MartijnScheer/Synthesizer/Documentatie 2024-2025/Input/Presentatie PCB Ontwerp Van Rick smelt en Patrick van Ommen.pdf

# Pulse soundworks

# Project synthesizer PCB Ontwerp

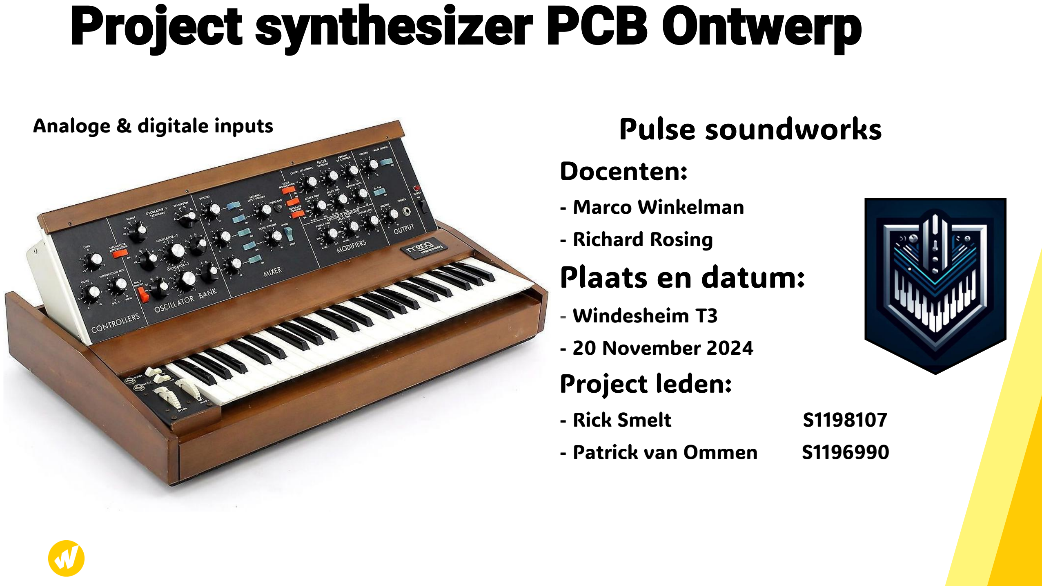
[picture p133: page 1]

# Docenten:

## - Marco Winkelman - Richard Rosing

# Plaats en datum:

## - Windesheim T3 - 20 November 2024

# Project leden:

- Rick Smelt | S1198107
- Patrick van Ommen | S1196990

## Analoge & digitale inputs

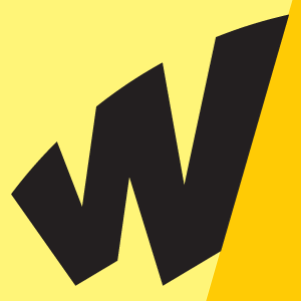
[picture p134: figure]

# Herhaling

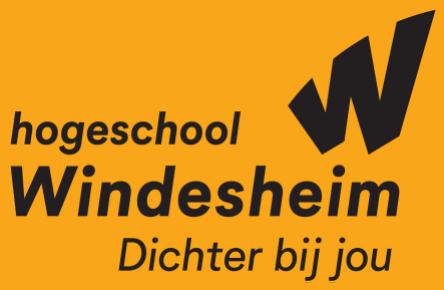
[picture p135: figure]

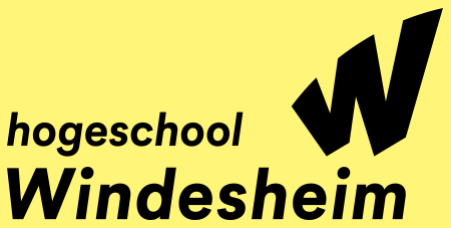
[picture p136: figure]

# wat is de opdracht?

❑Het ontwerpen en bouwen van een modulaire synthesizer.

### ❑ Er moet een analoge input en een midi input worden gemaakt en deze moet aangesloten

worden.
❑ Voor de analoge input wordt een keyboard gemaakt. En voor de midi input zal het digitale signaal worden omgezet naar een analoog signaal.
❑ Uit beide inputs zal een gate signaal komen en een toonhoogte. Deze beide signalen moeten

### naar de volgende modules:

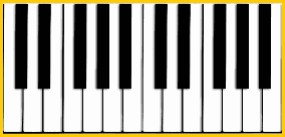
[picture p137: figure]
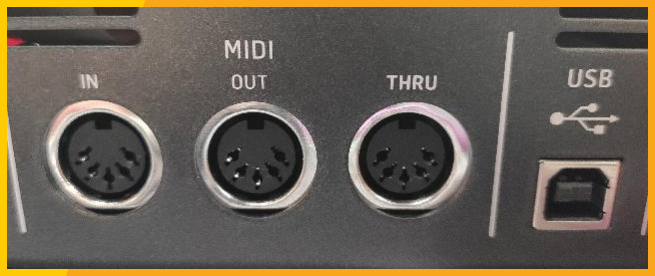
[picture p138: figure]

- ADSR- module
- Sequenser
- oscillator

# Achtergronden

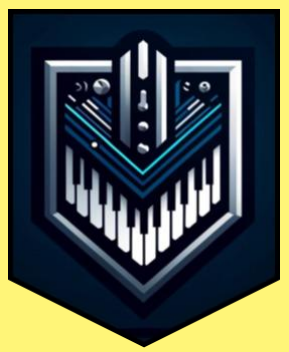
[picture p139: figure]

# Doelstelling:

# Project resultaten

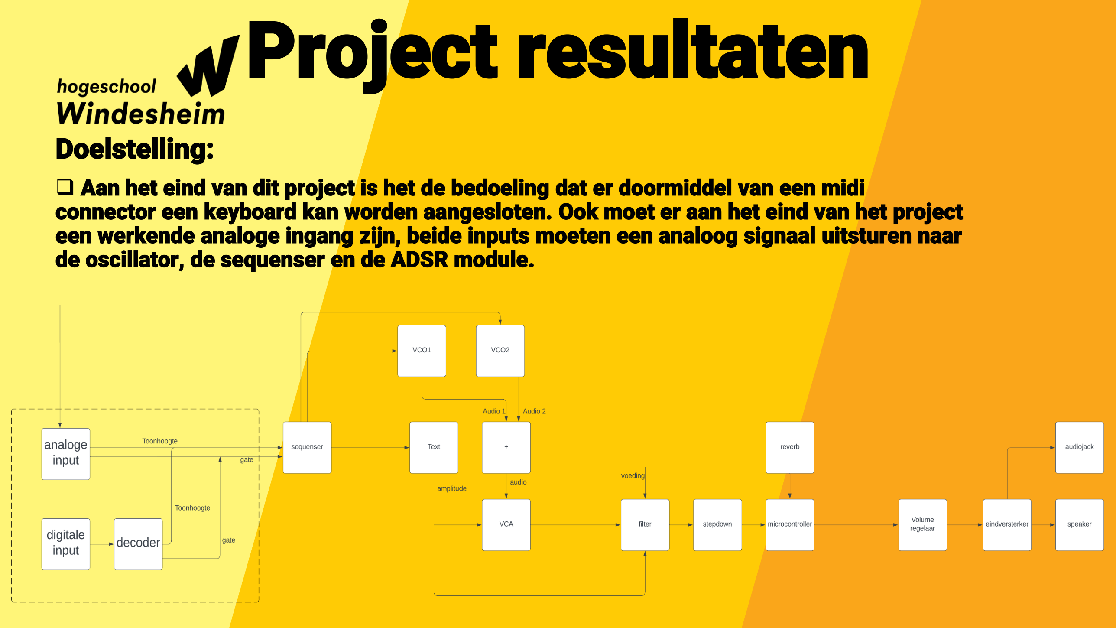
[picture p140: page 4]

## ❑ Aan het eind van dit project is het de bedoeling dat er doormiddel van een midi connector een keyboard kan worden aangesloten. Ook moet er aan het eind van het project een werkende analoge ingang zijn, beide inputs moeten een analoog signaal uitsturen naar

de oscillator, de sequenser en de ADSR module.

# Eisen Analoge input

Functioneel of niet functioneel | eis
Functioneel | Al is een toets ingedrukt en er word een volgende toets ingedrukt dient deze toon te worden afgespeeld en de initiële toon te stoppen.
Functioneel | Minimaal 1 octaaf aan toetsen waarbij er 4 octaven kunnen worden afgespeeld
Functioneel | Een analoog signaal voor de toonhoogte.
Functioneel | Een gate signaal moet worden verstuurd zodra een toets op het keyboard is ingedrukt of is losgelaten, dit signaal is uit: 0V en aan 3.3V
Functioneel | 1 octaaf krijgt een range van 1 volt.
Niet functioneel | Geen aanslag gevoeligheid
Niet functioneel | Een maximaal bedrag van 50 euro
Niet functioneel | De module moet samen kunnen werken met de andere groepen.
Niet functioneel | Het moet veilig en gemakkelijk in gebruik zijn

# Eisen Digitale input

Functioneel of niet functioneel | eis
Functioneel | Al is een toets ingedrukt en er word een volgende toets ingedrukt dient deze toon te worden afgespeeld en de initiële toon te stoppen.
Functioneel | De decoder zet het digitale midi signaal om naar een analoog signaal voor de toonhoogte.

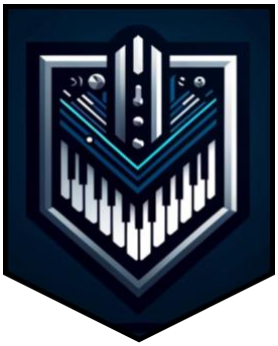
[picture p141: figure]

Functioneel | Een gate signaal moet worden verstuurd zodra een toets op het keyboard is ingedrukt of is losgelaten, dit signaal is uit: 0V en aan: 3.3V
Functioneel | Na de midi connector moet het digitale signaal worden verstuurt naar een decoder deze zet het midi signaal om naar een analoge signaal die overeen komt met het analoge input signaal
Functioneel | De midi input moet voor het grootste gedeelte voldoen aan het NEN-EN-INC 63035 protocol, daaronder valt dus geen aanslag gevoeligheid en opslaan van het signaal.
Niet functioneel | Geen aanslag gevoeligheid
Niet functioneel | Een maximaal bedrag van 50 euro
Niet functioneel | De module moet samen kunnen werken met de andere groepen.
Niet functioneel | Het moet veilig en gemakkelijk in gebruik zijn

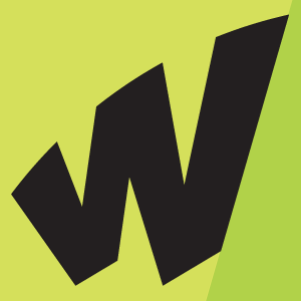
[picture p142: figure]

# PCB

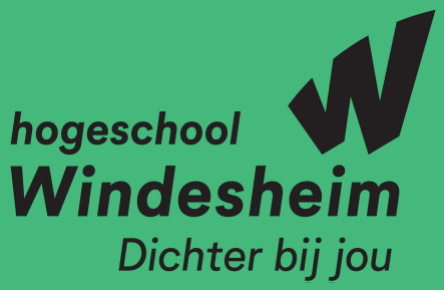
[picture p143: figure]

# SCHEMA PCB

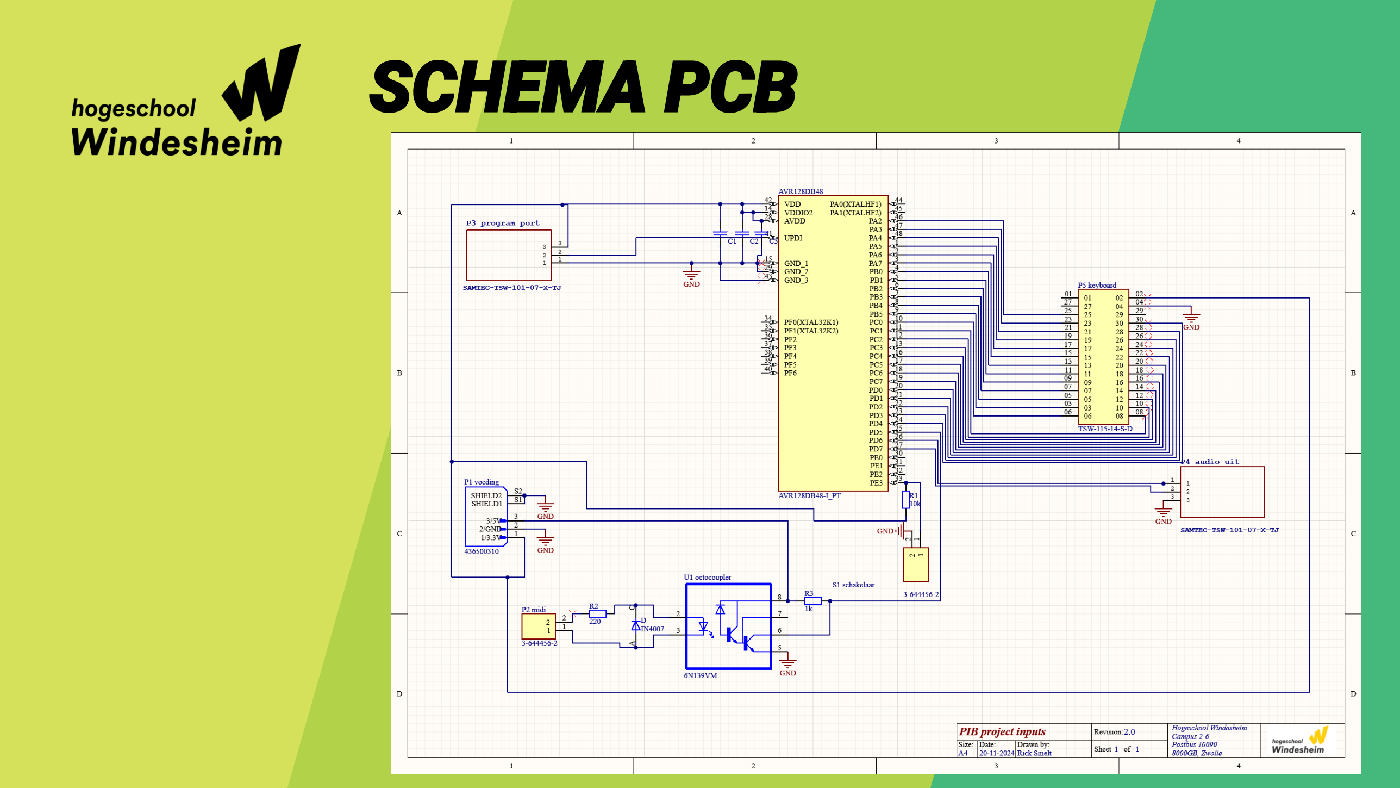
[picture p144: page 8]

DESIGN 2D | DESIGN 3D

# PCB DESIGN

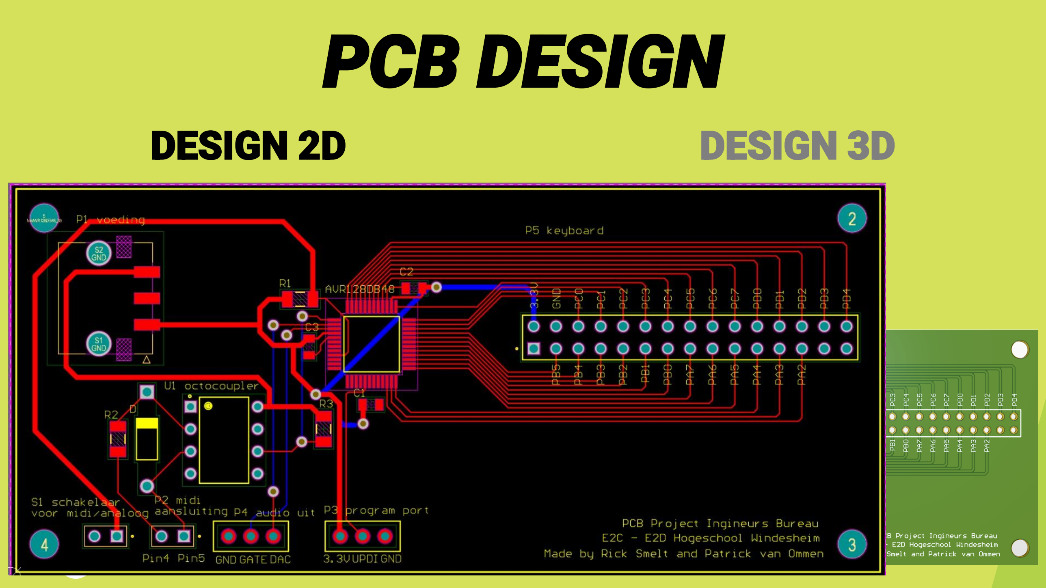
[picture p145: page 9]

DESIGN 2D | DESIGN 3D

# PCB DESIGN

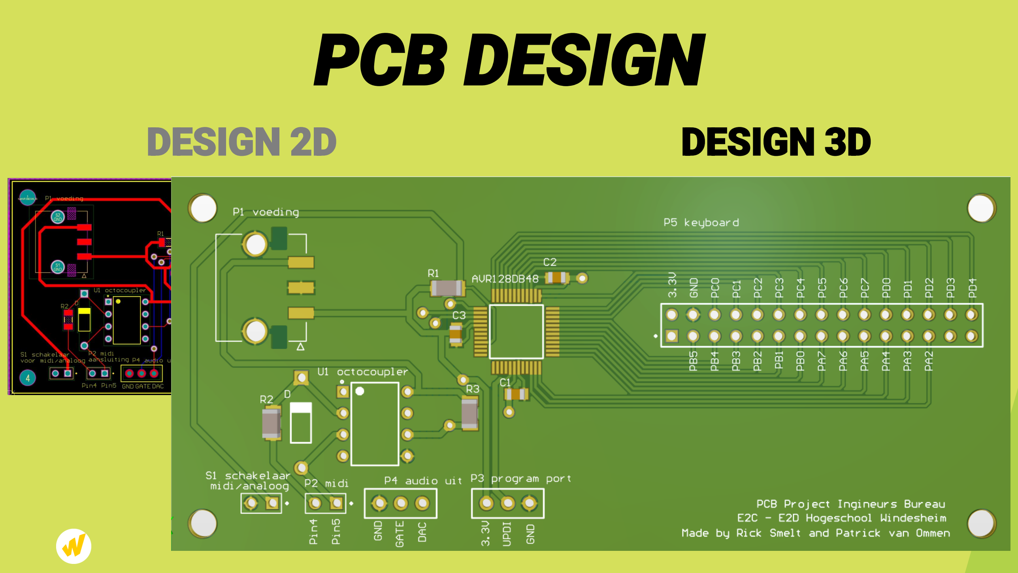
[picture p146: page 10]

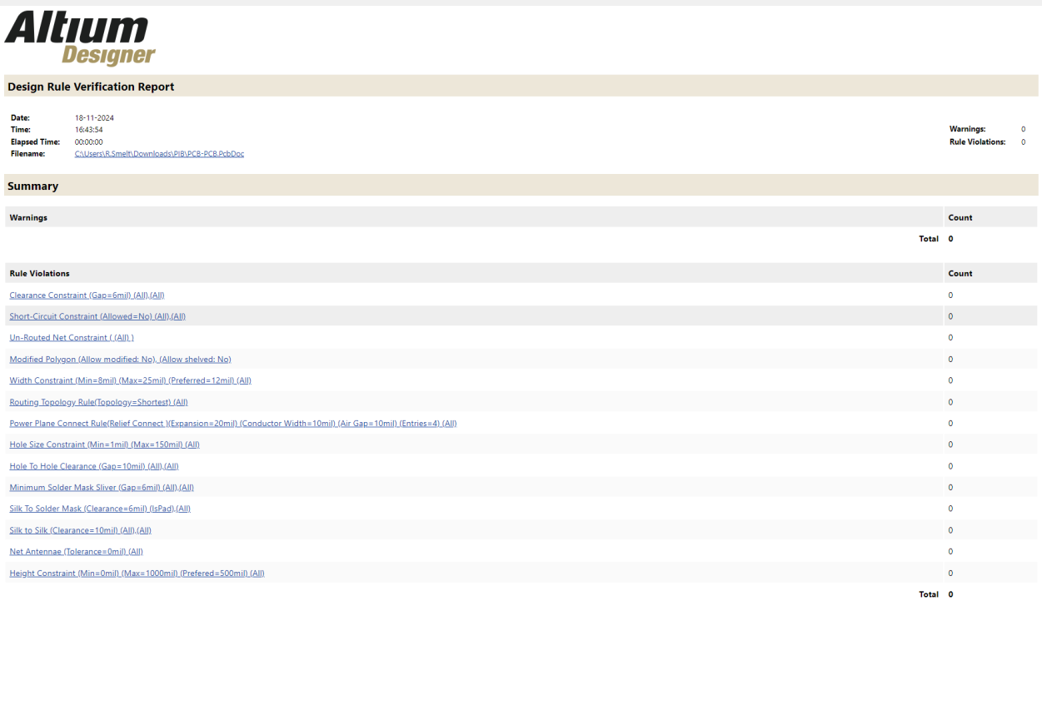
[picture p147: figure]

# - Alle rules die de fabrikant had aan het PCB zijn opgenomen in de rules van altium. De foto hiernaast geeft aan dat het PCB aan alle rules voldoet die de

fabrikant heeft opgesteld.

# DESIGN RULE CHECK / DESIGN RULE CHECK FABRIKANT

# KEUZE VAN PLAATSING COMPONENTEN

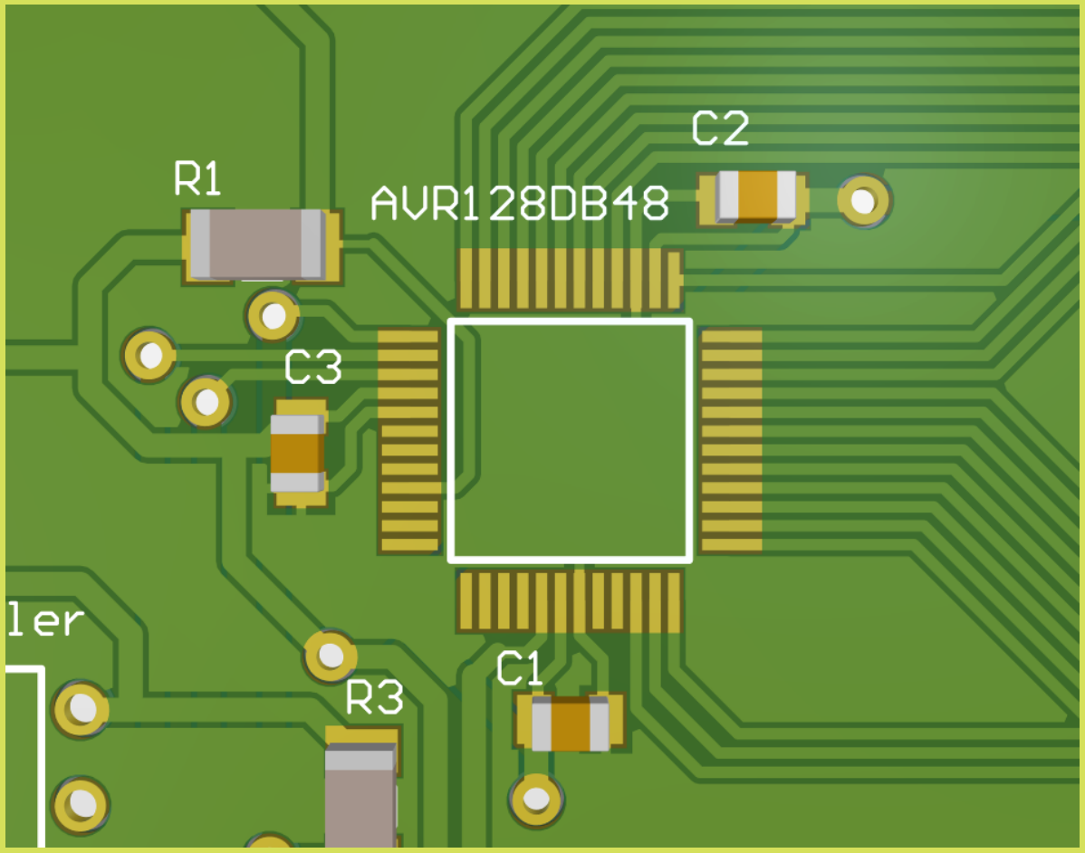
[picture p148: figure]

# KEUZE VAN PLAATSING COMPONENTEN

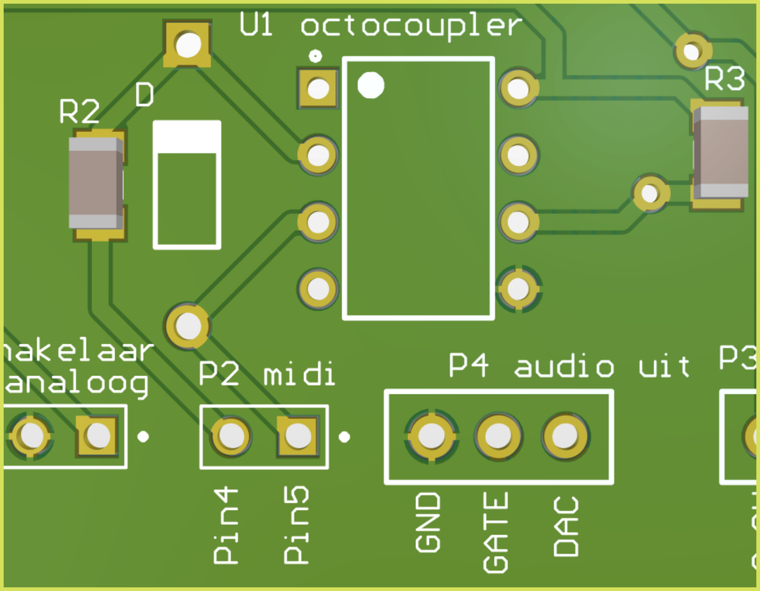
[picture p149: figure]

# KEUZE VAN PLAATSING COMPONENTEN

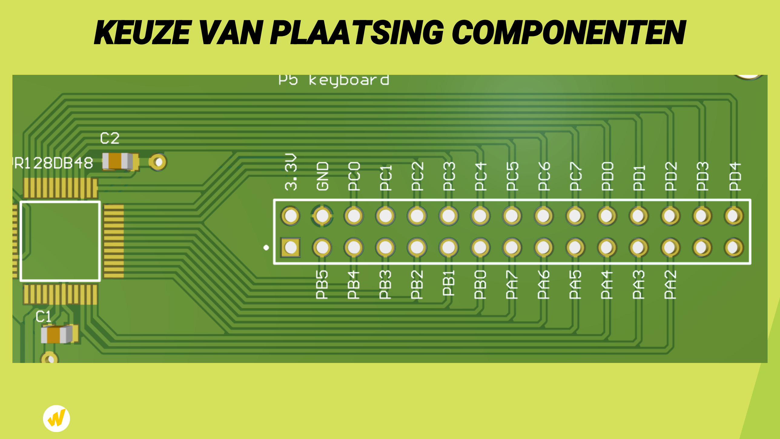
[picture p150: page 14]
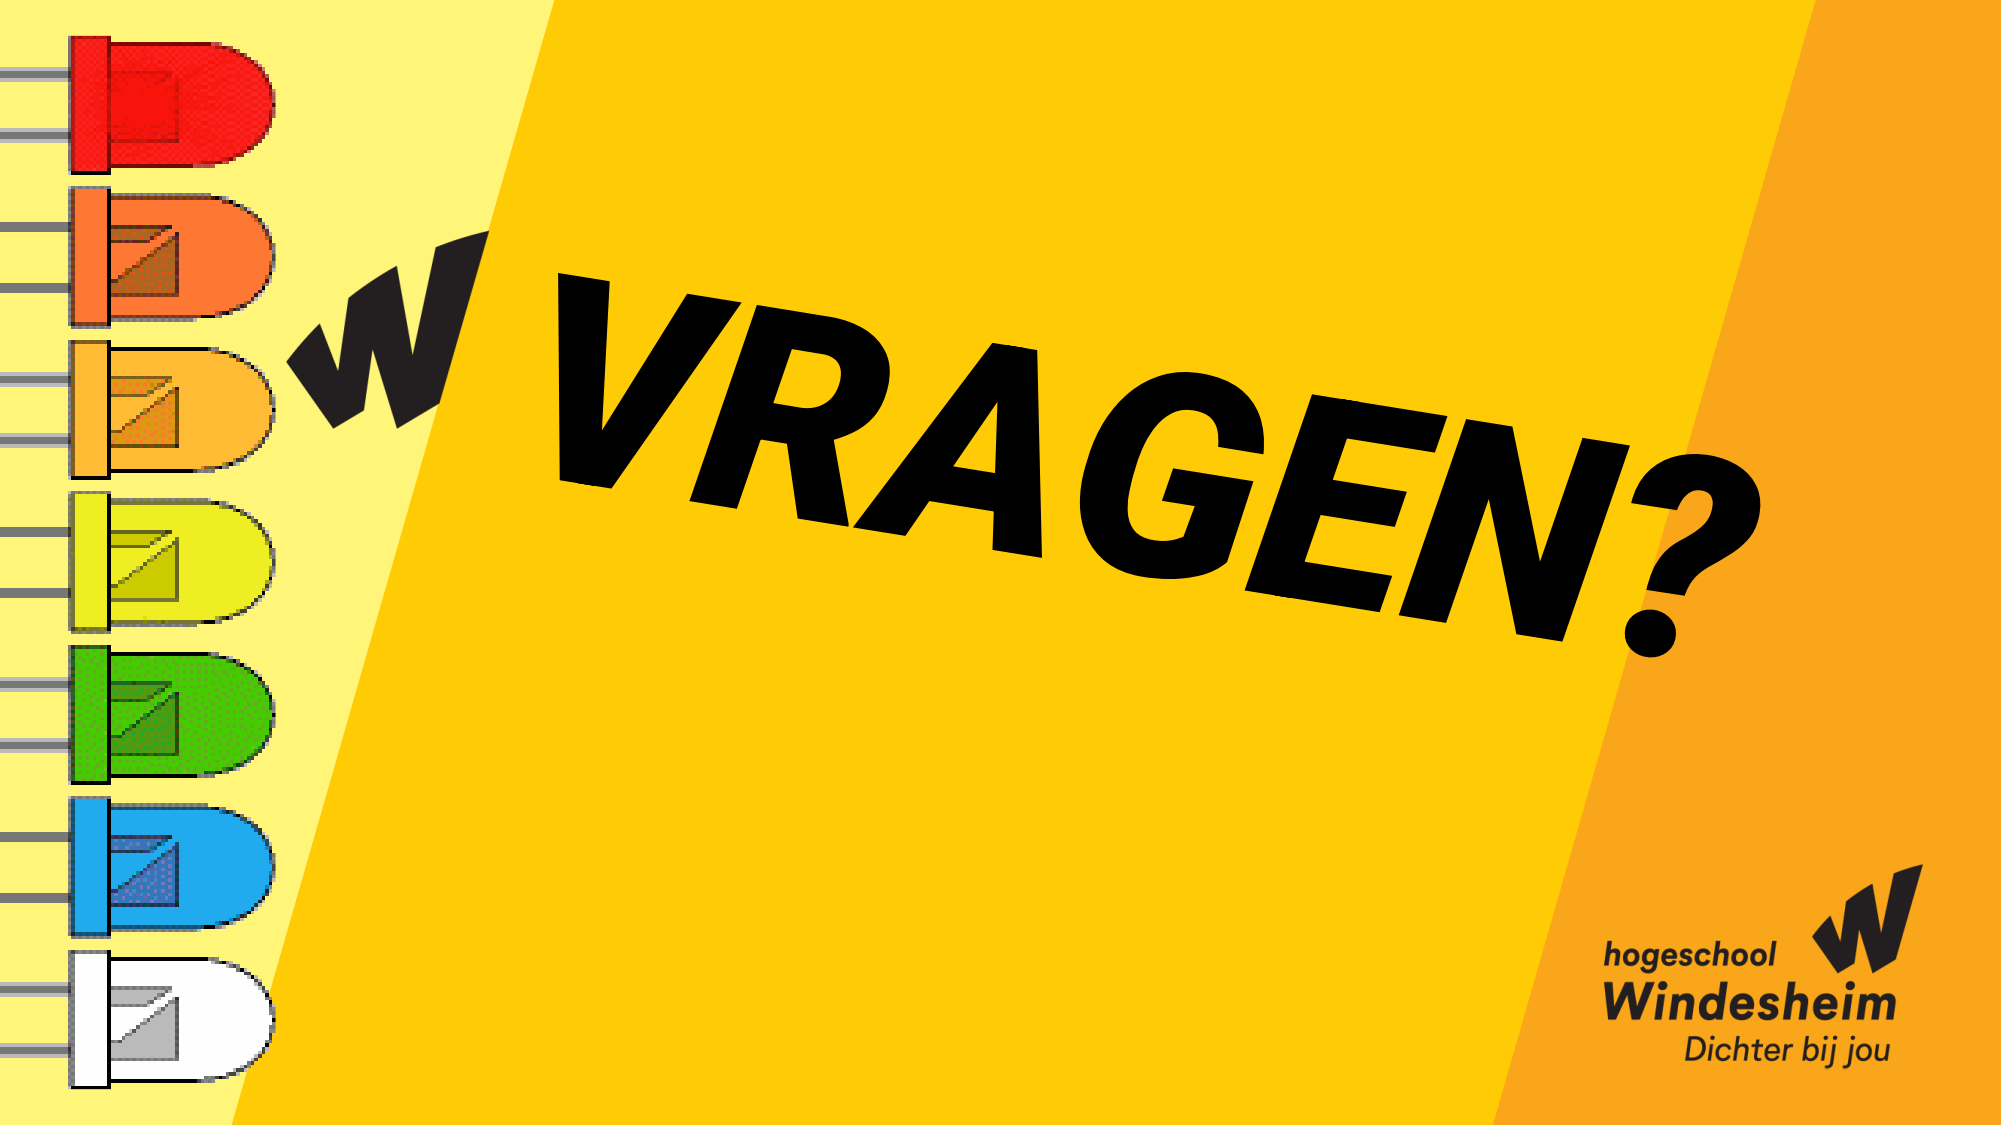
[picture p151: page 15]
