MartijnScheer/Synthesizer/Documentatie 2024-2025/Power amplifier + Power supply/Ontwerp/PIB Ontwerp Eindversterker en Voeding.pdf

# Concept

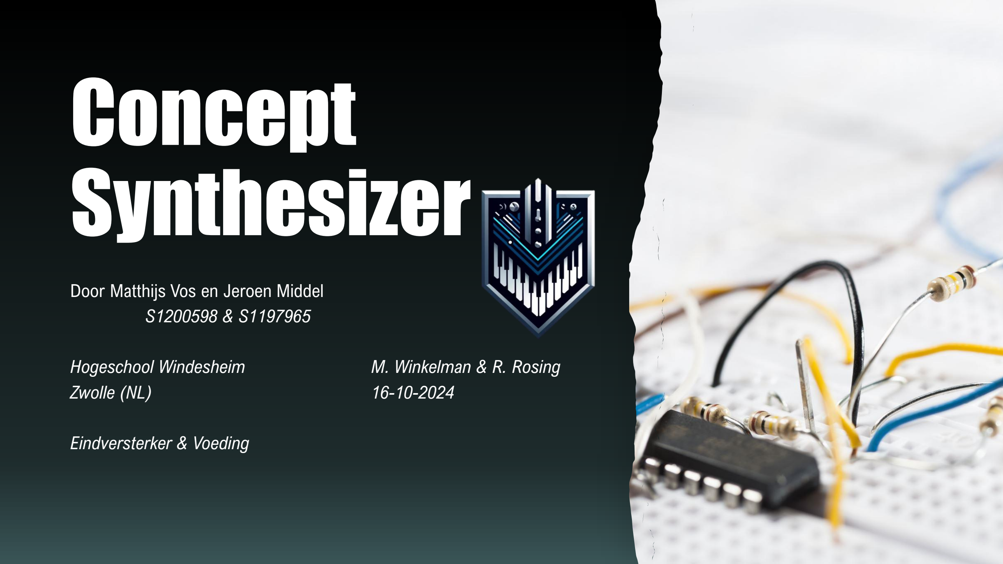
[picture p170: page 1]

# Synthesizer

### Door Matthijs Vos en Jeroen Middel

S1200598 & S1197965

Hogeschool Windesheim | M. Winkelman & R. Rosing
Zwolle (NL) | 16-10-2024

### Eindversterker & Voeding

# Plan van Eisen, Versterker

Eisen - Moet genoeg kunnen versterken voor een externe speaker van 8 ohm (functioneel) - Minimaal vermogen van de eindversterker is 1W eff (functioneel) - De modules voor de eindersterker moeten worden beschermd (niet-functioneel) - De gebruiker moet het volume kunnen aanpassen (functioneel) - De eindversterker mag niet te warm worden (passief, actief) (niet-functioneel) - Vervorming (1% harmonisch)(niet-functioneel)

## Wensen

- Meerdere soorten outputs (Speaker,

## audiojack) (niet-functioneel) - Over current protection voor de eindversterker en de voeding (niet-functioneel) - Beide modules de voeding en de versterker zo energiezuinig maken met minimale verliezen (niet-functioneel) - Beide modules zo compact mogelijke maken (niet-functioneel)

16-10-2024

# Ontwerp Eindversterker

## - Ingangsspanning maximaal 5 Vpp

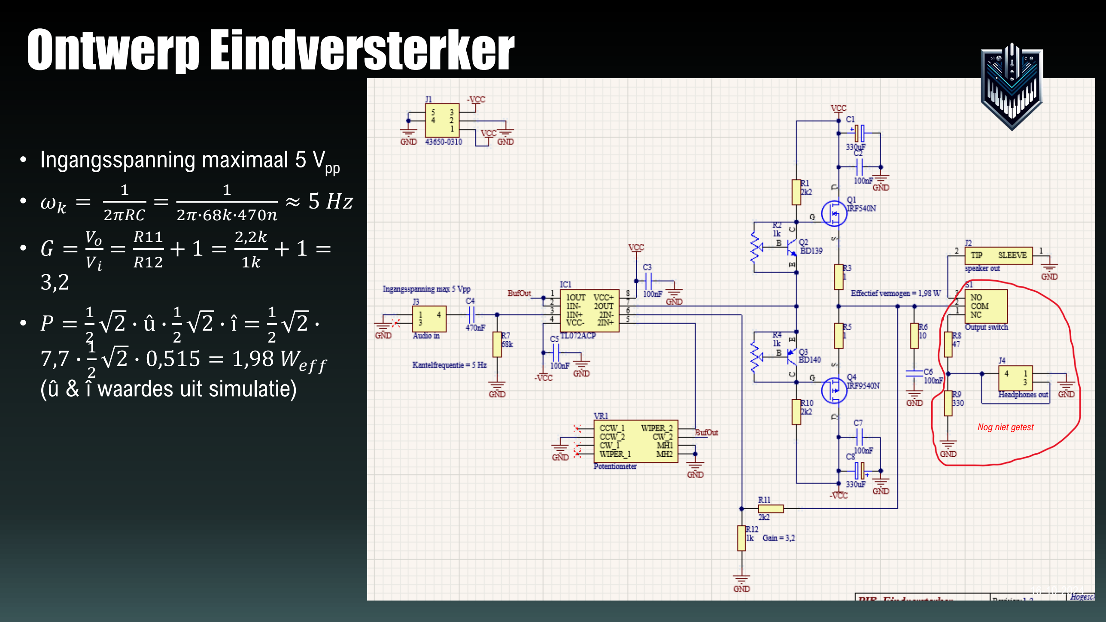
[picture p171: page 3]

- ωk =

1
2πRC

=

1
2π∙68k∙470n

≈ 5 Hz

- G =

Vo
Vi

=

R11
R12

+ 1 =

2,2k
1k

+ 1 =
3,2
- P =

1
2

2 ∙ û ∙

1
2

2 ∙ î =

1
2

2 ∙
7,7 ∙

1
2

## 2 ∙ 0,515 = 1,98 Weff

## (û & î waardes uit simulatie)

Nog niet getest

Kenmerk | MOSFET | BJT
Type | Spannings-gestuurd | Stroom-gestuurd
Besturing | Bestuurd door spanning op de gate | Bestuurd door basisstroom
Ingangsimpedantie | Hoog (meestal in de megaohms) | Laag (meestal in de kiloohms)
Stroomversterking | Kan zeer hoog zijn (afhankelijk van type, bv. N-kanalen of P-kanalen) | Lager, afhankelijk van de hFE-waarde (50 -500)
Verlies (Efficiency) | Lager bij hoogfrequente toepassingen | Hoger door basisstroom
Snelle schakeling | Sneller, vooral bij hoge frequenties | Langzamer vergeleken met MOSFET
Vermogensverlies | Lager omdat er minder inputstroom nodig is | Hoger vanwege hogere inputstroom
Thermisch gedrag | Minder gevoelig voor temperatuurvariaties | Gevoeliger voor temperatuurvariaties
Gebruik in vermogensschakelingen | Zeer geschikt voor hoge vermogens | Minder geschikt voor hoge vermogens
Kosten | Vaak duurder | Goedkoper
Toepassingen | Voornamelijk gebruikt in vermogenselektronica (bijv. voedingen, converters) | Gebruikt in lage-vermogenselektronica (bijv. versterkers)
Controle op aan/uit-stand | Eenvoudiger door de spanning op de gate | Moeilijker vanwege continue basisstroom nodig
Beschikbaarheid van modellen | N-kanaal en P-kanaal | NPN en PNP
Complexiteit van schakeling | Eenvoudiger ontwerp (minder componenten nodig) | Complexer ontwerp (meer componenten nodig)
Ruisgevoeligheid | Minder gevoelig voor ruis | Meer gevoelig voor ruis | 16-10-2024

# Vergelijk transistoren

# Vergelijk Bias

Type Diode | Werking | Kenmerken | Toepassingen | Complexiteit
Normale diode | Geleidt stroom in één richting (van anode naar kathode) en blokkeert in de andere richting | Voorwaartse spanning nodig om te geleiden (meestal 0,7V voor silicium, 0,3V voor germanium). Hoge doorslagspanning in omgekeerde richting. Laag spanningsverlies. | Gelijkrichtcircuits (AC naar DC omzetting), beveiliging tegen omgekeerde stroom, signaaldetectie en schakeling in elektronica. | Eenvoudig
Zenerdiode | Werkt als een normale diode in de voorwaartse richting, maar laat stroom door in omgekeerde richting bij een specifieke zenerspanning (bv. 5V) | Zenerspanning bepaalt de omgekeerde doorslagspanning. Stabiel bij deze spanning. Kan als spanningsreferentie werken en gecontroleerde omgekeerde stroom geleiden. | Spanningsreferenties in voedingen, beveiliging tegen spanningspieken, spanningsclamping, stabilisators in spanningsregelaarcircuits. | Matig
Variabele zenerdiode (VDR) | Gedraagt zich als een zenerdiode, maar de zenerspanning kan worden gevarieerd door een externe controle (zoals een potmeter of spanning) | Verstelbare zenerspanning afhankelijk van externe instellingen. Flexibele spanningsreferentie. Mogelijkheid om dynamisch de gewenste klemspanning in te stellen. | Instelbare spanningsregelaars, bescherming in schakelingen met veranderlijke spanningen, dynamische spanningsbeperking in voedingen of overspanningsbeveiligingen. | Complex

16

-10

-2024

# Vergelijk Spanningsversterker

Type Versterker | Werking | Kenmerken | Toepassingen | Complexiteit
Operationele versterker (opamp) | Een geïntegreerde schakeling (IC) die signalen versterkt door een verschilspanning tussen twee ingangen (inverting en non-inverting) te verwerken. | Zeer hoge versterkingsfactor. Hoge ingangsimpedantie, lage uitgangsimpedantie. Stabiele prestatie met weinig drift. Flexibel inzetbaar in meerdere configuraties (inverterend, niet-inverterend, comparator). | Audioversterkers, filters, signaalverwerking, spanningsvolgers, comparatoren. | Eenvoudig tot matig (opbouw in IC).

Discrete
transistorversterker

Gebruikt individuele
transistors (zoals BJT's
of MOSFET's) om
stroom te regelen en
een ingangssignaal te
versterken.

Configuratie kan flexibel
worden opgebouwd met
losse componenten.
Middelmatige tot hoge
versterkingsfactor,
afhankelijk van de
schakeling. Hoger
stroomverbruik en grotere
componenten. Meerdere
transistortrappen nodig voor grote versterking.

Basisaudioversterkers, RFversterkers,
vermogensversterkers in
vermogenstoepassingen.

Complex (moet zelf
ontworpen en
opgebouwd
worden).

# Controle eisen, Versterker

## Controle - Er komt het juiste geluid uit de speaker - Peff = 1,98 W in simulatie - Peff = … W IRL - Er zit een buffertrap in voor de versterker

## - Er zit een potmeter om het volume te regelen

## - Het breadbord smelt niet onder de schakeling weg

## - Er is geen vervorming op de scoop te zien

Eisen - Moet genoeg kunnen versterken voor een externe speaker van 8 ohm (functioneel) - Minimaal vermogen van de eindversterker is 1W eff (functioneel) - De modules voor de eindersterker moeten worden beschermd (niet-functioneel) - De gebruiker moet het volume kunnen aanpassen (functioneel) - De eindversterker mag niet te warm worden (passief, actief) (niet-functioneel) - Vervorming (1% harmonisch)(niet-functioneel)

# Plan van Eisen, Voeding

## Eisen

- Moet verschillende voltages kunnen leveren aan verschillende modules in de synthesizer (functioneel) - Moet symmetrisch voeding kunnen leveren van minimaal –10 tot +10 Volt (functioneel) - Moet asymmetrisch voeding kunnen leveren van minimaal +3,3 Volt (functioneel) - De voeding moet minimaal 80 mAmpère kunnen leveren aan elk van de modules (functioneel) - De voeding moet aan en uit kunnen worden gezet door de gebruiker (functioneel)

- De voeding mag niet te warm worden (passief,

## actief) (niet-functioneel) - Moet een lage rimpelspanning hebben (< 50mV) (niet-functioneel)

## - Eindversterker voeding minimaal 0.5 A (functioneel)

## Wensen

## - Over current protection voor de eindversterker en de voeding (niet-functioneel)

## - Beide modules de voeding en de versterker zo energiezuinig maken met minimale verliezen (niet-functioneel) - Beide modules zo compact mogelijke maken (niet-functioneel)

# Ontwerp Voeding

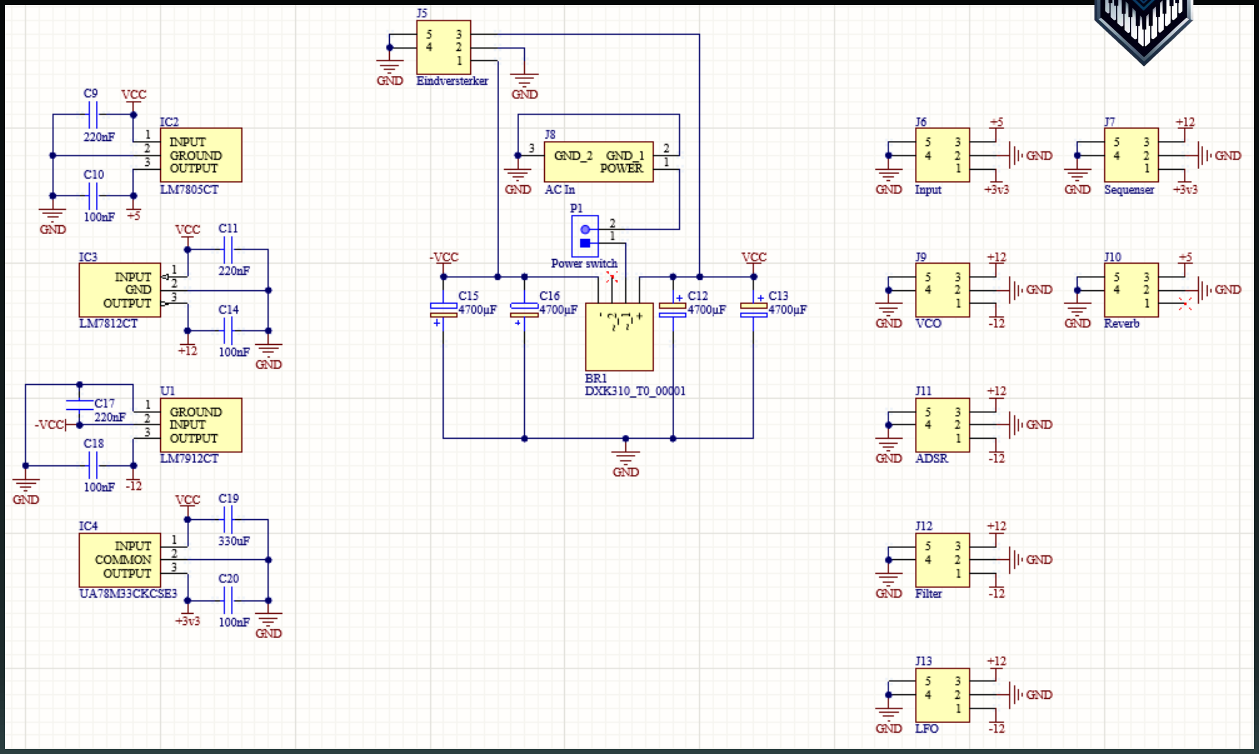
[picture p172: figure]

# Vergelijk type gelijkrichters

Type Gelijkrichter | Werking | Kenmerken | Toepassingen | Complexiteit
Enkelzijdige gelijkrichter | Gebruikt één diode om alleen de positieve halve golf van een wisselspanning door te laten, terwijl de negatieve helft wordt geblokkeerd. | Eenvoudig ontwerp. Verliest de helft van het AC -signaal (negatieve halve golf). Gemiddelde gelijkspanning is lager, en er is meer rimpel in de uitgangsspanning. Alleen de positieve halve golf wordt gebruikt, waardoor de efficiëntie lager is. | Lage -vermogenstoepassingen, eenvoudige voedingen, basis AC naar DC omzettingen. | Eenvoudig.
Dubbelzijdige gelijkrichter (2 diodes, middenaftakking) | Gebruikt twee diodes in combinatie met een transformator met een middenaftakking om zowel de positieve als de negatieve halve golf van de wisselspanning om te zetten in een gelijkspanning. | Maakt gebruik van een transformator met een middenaftakking, waarbij elke diode één helft van de wikkeling verwerkt. Minder componenten (2 diodes), maar de piekspanning is de helft van de secundaire spanning. | Voedingen met lagere vermogens, toepassingen waar een transformator met middenaftakking beschikbaar is. | Matig.
Dubbelzijdige gelijkrichter (4 diodes, brugschakeling) | Gebruikt vier diodes in een brugschakeling om zowel de positieve als de negatieve halve golf van de wisselspanning om te zetten in gelijkspanning. | Geen middenaftakking nodig. Volledige AC -golf wordt gebruikt, wat zorgt voor hogere efficiëntie en een hogere gemiddelde gelijkspanning. Hogere uitgangsspanning met minder rimpel. Meer componenten (4 diodes). | Voedingen met hogere vermogens, efficiëntere AC naar DC omzettingen, toepassingen waar een stabiele gelijkspanning nodig is. | Complex.

16

-10

-2024

# Controle Eisen, Voeding

## Eisen

- Moet verschillende voltages kunnen leveren aan verschillende modules in de synthesizer (functioneel) - Moet symmetrisch voeding kunnen leveren van minimaal –10 tot +10 Volt (functioneel) - Moet asymmetrisch voeding kunnen leveren van minimaal +3,3 Volt (functioneel) - De voeding moet minimaal 80 mAmpère kunnen leveren aan elk van de modules (functioneel) - De voeding moet aan en uit kunnen worden gezet door de gebruiker (functioneel)

- De voeding mag niet te warm worden (passief,

## actief) (niet-functioneel) - Moet een lage rimpelspanning hebben (< 50mV) (niet-functioneel)

## - Eindversterker voeding minimaal 0.5 A (functioneel)

Controle - Kan verschillende voltages leveren - Kan symmetrisch -12 tot +12 Volt leveren - Kan asymmetrisch +5 Volt leveren - Kan 80 mAmpère leveren aan alle modules binnen de synthesizer - Er is een aan en uit knop aanwezig - Het breadbord/breadbord kabels smelten niet - De rimpelspanning is maximaal 400mV - De eindversterker kan 0.5 A krijgen van de voeding

# Demo!!
