MartijnScheer/Synthesizer/Documentatie 2024-2025/README

Deze mappen bevatten de documentatie van de modules zoals ze waren in 2024-2025. 
Wees bewust dat deze documentatie op het moment van lezen kan zijn verouderd door mogelijke veranderingen in de synthesizer.
