MartijnScheer/Synthesizer/Documentatie Minor Project Synthesizer Hidde Huysmans & Martijn Scheer 2026/README

Documentatie van het Minor Project Synthesizer Hidde Huysmans & Martijn Scheer.
