MartijnScheer/Synthesizer/Documentatie Minor Project Synthesizer Hidde Huysmans & Martijn Scheer 2026/GitHub Documentatie/Readme

Documentatie van de GitHub zoals deze door ons is ingericht aan het einde van het 2026 elektronica project, dit mapje is puur ter documentatie voor het nakijken.
Voor projectgroepen is deze map niet van belang.
