MartijnScheer/Synthesizer/Documentatie 2024-2025/Filter/READ ME.txt

Om het bestand te kunnen openen
- Ga naar: https://app.diagrams.net/
- Druk op "bestaand diagram openen".
- Selecteer het .drawio bestand in deze map.
