MartijnScheer/Synthesizer/Documentatie Minor Project Synthesizer Hidde Huysmans & Martijn Scheer 2026/Software/Readme

De software per 06-2026. De laatste versie die wij hebben bewerkt.
