MartijnScheer/Synthesizer/Documentatie Minor Project Synthesizer Hidde Huysmans & Martijn Scheer 2026/Vooronderzoekje polyfoon/readme

Vooronderzoekje voor het omzetten van de huidige inputmodule naar een polyfoon systeem
