MartijnScheer/Synthesizer/Documentatie 2024-2025/LFO/README

Bestanden voor de LFO module gemaakt door Ruben Boeve
