MartijnScheer/Synthesizer/Documentatie 2024-2025/Sequencer/README

Bestanden voor de Sequencer module gemaakt door Roelof Zijda en Reinout Strating
