MartijnScheer/Synthesizer/Documentatie 2024-2025/Input/README

Bestanden voor de input module van de Synthesizer gemaakt door Rick Smelt en Patrick van Ommen
