MartijnScheer/Synthesizer/Documentatie 2024-2025/VCO/VCO concepten Ralph en Thijn V2.pptx

## Modulaire Synthesizer, VCO Concepten.

Thijn Berkhoff – 1198746
Ralph Hänninger – 1197535
Begeleid door Marco Winkelman

Mijn startpagina

25-9-2024
Zwolle

## Inhoudsopgave

Inleiding
Eisen en beperkingen
Conceptoplossing
Vergelijking concepten

## Inleiding

Opdracht:
Samen met de andere modules een synthesizer maken.
Doelstelling:
Het ontwerpen en designen van een volledige VCO module

## Slide 4

Eisen | functioneel | Niet-functioneel | verplicht | optioneel | prioriteit
1v/octaaf | x | | x | | 1
stroombeveiliging | | x | x | | 1
2 uitgangssignalen | x | | x | | 1
Bescherming in- en outputs | | x | x | | 1
PCB zo klein mogelijk | | x | | x | 3
Blok, driehoek en zaagtand signaal | x | | x | | 2
Moet samenwerken met andere modules | x | | x | | 1
Elektronica moet zichtbaar zijn | | x | x | | 3
Enige middelen tegen warmtevervoming | | x | | X | 3
Instelbare lineariteit en zaagsignaal | x | | | x | 2

## Slide 5

Beperkingen

Stroom en spanningslimieten.
Budget van 50 euro.
Geen kant en klare componenten. (devboards, Modules ETC)
Uiteindelijke afmetingen van het volledige design.

## Concept oplossingen

- Concept 1

Zaagtand oscillator als kern, andere signalen worden daaruit gemoduleerd.
Gebaseerd op een comparator / integrator opamp schakeling.

- Concept 2

Relaxation oscillator als kern, zaagtand wordt gemoduleerd uit blok of driehoek.
Geïnspireerd door “Electronics a system approach” van Neil Storey

## Concept 1

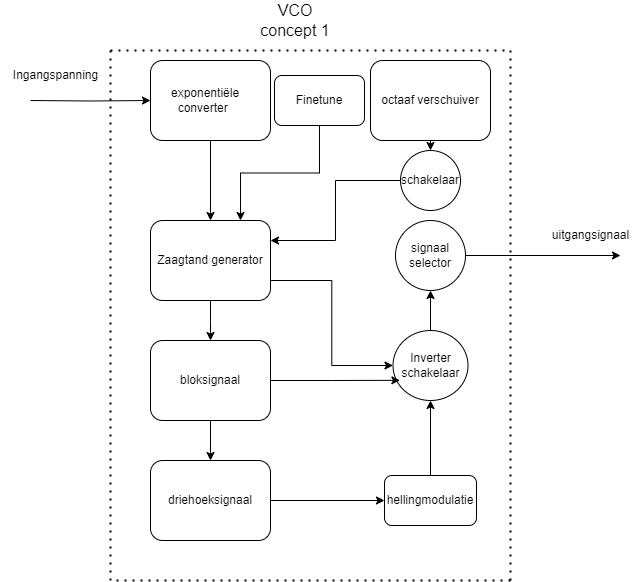
[picture p173: figure]

## Conceptschakeling 1

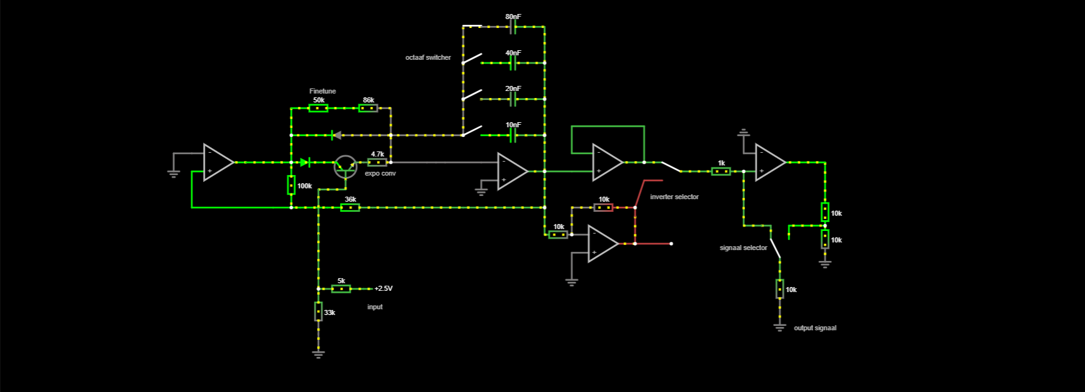
[picture p174: figure]

- Gesimuleerd op falstad.com
- Mist nog driehoek generator en hoekmodulatie
- Voldoet nog niet volledig aan eisen maar dat zou veranderd kunnen worden

## Concept 2

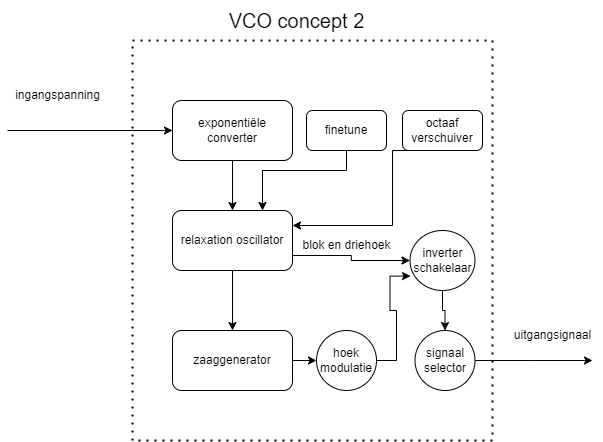
[picture p175: figure]

## Vergelijking concepten

- Concept 1

- Gebruikt 2 opamps voor de kern
- Iets ingewikkelder design
- Finetune en zaagsignaal makkelijker te bereiken
- Flexibeler door zaagsignaal als kern
- Onder 50 euro

- Concept 2

- Gebruikt 1 opamp voor de kern
- Wat minder ingewikkeld
- Zaagsignaal en finetune moeilijker te bereiken
- Minder flexibel want blok- en driehoeksignaal als kern
- Onder 50 euro

## Voorkeur Concept 1

- Zaagsignalen zijn makkelijker om te zetten naar andere signalen
- Flexibeler
- Conceptschakeling voldoet (bijna) aan de eisen
- Interessantere uitdaging
- Onder 50 euro

## Einde
