MartijnScheer/Synthesizer/Documentatie 2024-2025/Input/Systeemdossier uitleg.docx

# PCB Ontwerp

Dit zijn de Altium bestanden.

https://liveadminwindesheim-my.sharepoint.com/personal/s1198107_student_windesheim_nl/Documents/School/Jaar%202/Project%20synthensizer/Systeem%20Dossier/PIB%20PCB%20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

# CODE

Dit is het code bestand voor in MPLAB X IDE.

https://liveadminwindesheim-my.sharepoint.com/personal/s1198107_student_windesheim_nl/Documents/School/Jaar%202/Project%20synthensizer/Systeem%20Dossier/PIB_Code_Inp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

# Presentaties

## PVA

Dit is de PVA Presentatie.

https://liveadminwindesheim-my.sharepoint.com/personal/s1198107_student_windesheim_nl/Documents/School/Jaar%202/Project%20synthensizer/Systeem%20Dossier/Presentatie%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

## Inputs ontwerp

Dit is de ontwerp presentatie.

https://liveadminwindesheim-my.sharepoint.com/personal/s1198107_student_windesheim_nl/Documents/School/Jaar%202/Project%20synthensizer/Systeem%20Dossier/Presentatie%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

## Software Concepten

Dit is de Software Presentatie.

https://liveadminwindesheim-my.sharepoint.com/personal/s1198107_student_windesheim_nl/Documents/School/Jaar%202/Project%20synthensizer/Systeem%20Dossier/Presentatie%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

## PCB ontwerp

Dit is de PCB ontwerp Presentatie.

https://liveadminwindesheim-my.sharepoint.com/personal/s1198107_student_windesheim_nl/Documents/School/Jaar%202/Project%20synthensizer/Systeem%20Dossier/Presentatie%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

# Poster

Dit is de Poster.

https://liveadminwindesheim-my.sharepoint.com/personal/s1198107_student_windesheim_nl/Documents/School/Jaar%202/Project%20synthensizer/Systeem%20Dossier/Poster%20PIB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

# DAC waardes

Dit is een PDF bestand van de dacwaardes die we hebben gebruikt voor de code.

https://liveadminwindesheim-my.sharepoint.com/personal/s1198107_student_windesheim_nl/Documents/School/Jaar%202/Project%20synthensizer/Systeem%20Dossier/waardes%20vo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
