MartijnScheer/Synthesizer/Documentatie 2024-2025/Filter/Presentaties/Presentatie_PvA_Jens_Kuizenga_1175555.pptx

## Project Ingenieursbureau Plan van Aanpak


Opdrachtgever: Windesheim
Bedrijf: Pulse Soundworks
Datum: 11-09-’24
Diémo Rijsdijk: 1200704
Jens Kuizenga: 1175555

## Achtergronden

- De Organisatie
- De opdracht en opdeling
- De stakeholders

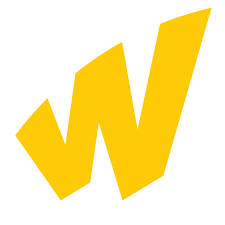
[picture p176: figure]
Afbeelding met muziek, piano, synthesizer, muziekinstrument

## Achtergronden

- - De organisatie

## Achtergronden

- - De opdracht en indeling

## Achtergronden

- - De stakeholders

## Projectresultaat

- Doelstelling
- Programma van eisen
- Probleemstelling
- Schema’s

## Projectresultaat: Doelstelling

- - SMART geformuleerd

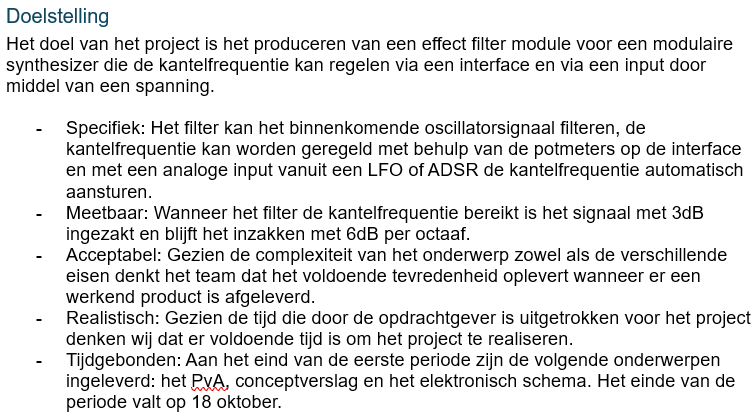
[picture p177: figure]

## Projectresultaat: Programma van eisen

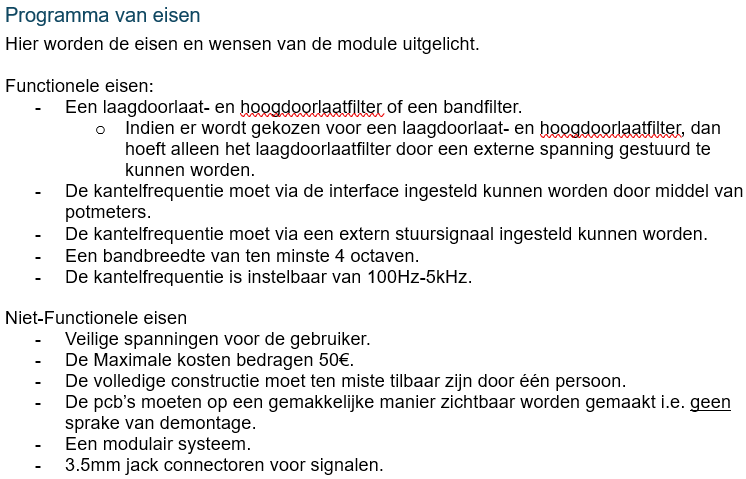
[picture p178: figure]

- Functionele- en niet functionele eisen
- Beperkingen

## Projectresultaat: Probleemstelling

- Probleemstelling
- Deelvragen

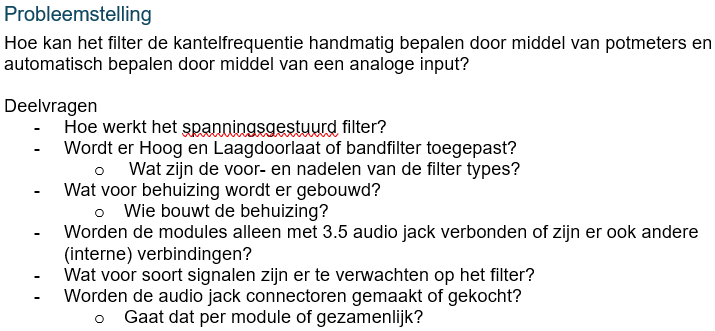
[picture p179: figure]

## Projectresultaat: Schema’s

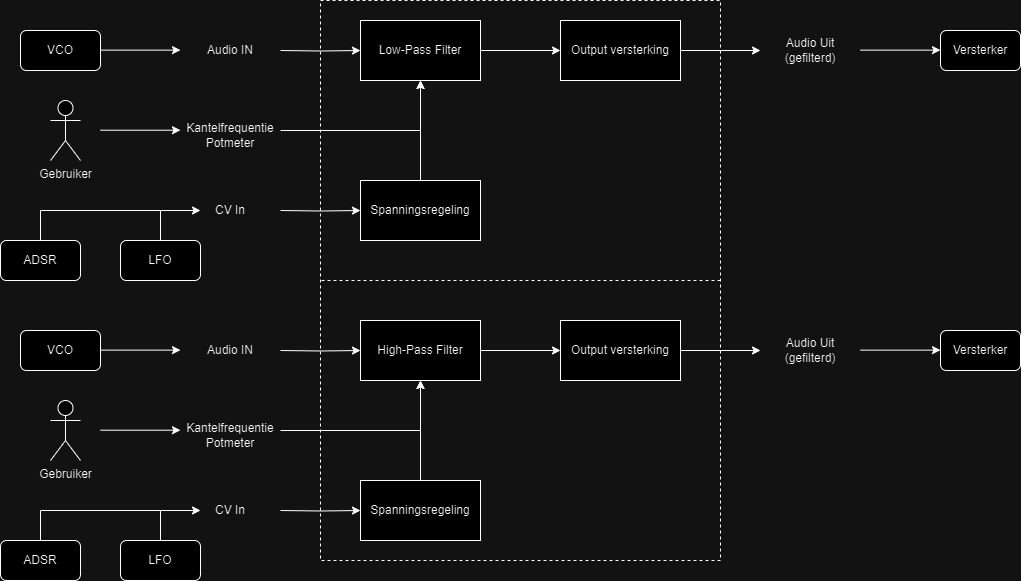
[picture p180: figure]

## Projectgrenzen en randvoorwaarden

- De afbakening
- Grensgevallen

## Projectgrenzen en randvoorwaarden

- - De randvoorwaarden

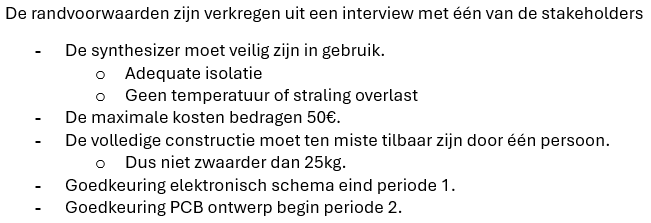
[picture p181: figure]

## Vragen?

- - Bedankt voor jullie aandacht
