MartijnScheer/Synthesizer/Documentatie 2024-2025/Power amplifier + Power supply/Concepten/PIB Concept Eindversterker en Voeding 2.0.pdf

# Concept


# Synthesizer

Door Matthijs Vos en Jeroen Middel
S1200598 & S1197965
Hogeschool Windesheim | M. Winkelman & R. Rosing
Zwolle (NL) | 25-09-2024

Eindversterker & Voeding

# Plan van Eisen, Versterker

Eisen
- Moet genoeg kunnen versterken voor een externe speaker van 8 ohm (functioneel)
- Minimaal vermogen van de eindversterker is 1W eff (functioneel)
- De modules voor de eindersterker moeten worden beschermd (niet-functioneel)
- De gebruiker moet het volume kunnen aanpassen (functioneel)
- De eindversterker mag niet te warm worden (passief, actief) (niet-functioneel)
- Vervorming (1% harmonisch)(niet-functioneel)

Wensen
- Meerdere soorten outputs (Speaker, audiojack) (niet-functioneel)
- Over current protection voor de eindversterker en de voeding (niet-functioneel)
- Beide modules de voeding en de versterker zo energiezuinig maken met minimale verliezen (niet-functioneel)
- Beide modules zo compact mogelijke maken (niet-functioneel)

2-10-2024

# Versterker Klasse verschillen


Versterker klasse | Efficiëntie | Geluidskwaliteit | Vervorming | Warmteproductie | Complexiteit | Toepassingen
Klasse A | Laag (~20-30%) | Zeer hoog | Zeer laag | Zeer hoog | Laag | High-end audio, studioapparatuur
Klasse B | Gemiddeld (~50-70%) | Lager dan Klasse A | Hoog (alleen rond de nul) | Gemiddeld | Gemiddeld | Budget audio, oudere versterkers
Klasse AB | Gemiddeld (~50-70%) | Tussen Klasse A en B | Laag (alleen rond de nul) | Gemiddeld | Gemiddeld/Hoog | Consumenten Hi-Fi, high-end audio
Klasse C | Zeer hoog (>80%) Niet geschikt voor | audio | Zeer hoog | Laag | Laag | Radio, RF-versterkers
Klasse D | Zeer hoog (~90-95%) | Goed | Matig tot laag (vroeger hoog) | Laag | Zeer hoog | Draagbare audio systemen

# Concepten Eindversterker

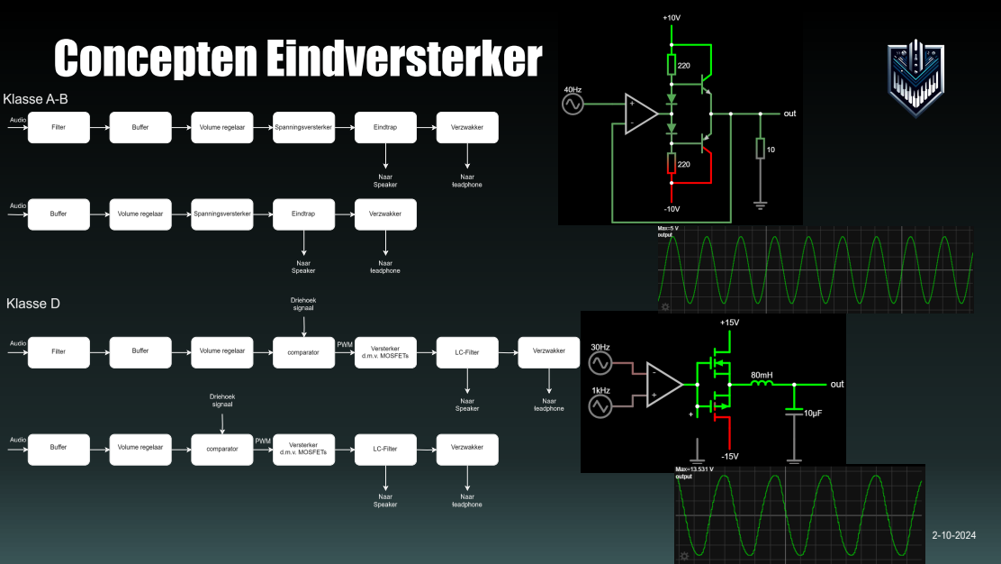
[picture p193: page 4]

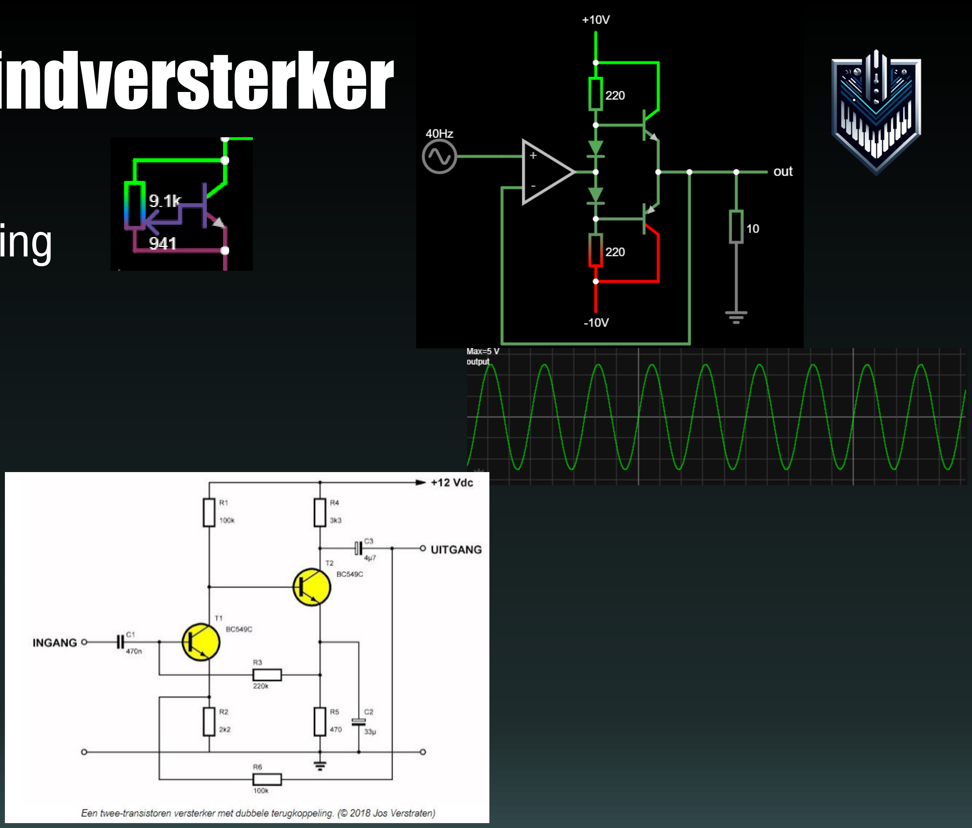
[picture p194: figure]

# Concepten A-B Eindversterker

## - Instelbare zener met thermische terugkoppeling i.p.v. normale zener

- BJT transistoren i.p.v.

## MOSFET's

- Verschilversterker i.p.v.

## Opamp

https://verstraten-elektronica.blogspot.com/p/twee-transistoren-versterkers.html

# Simulatie Eindversterker

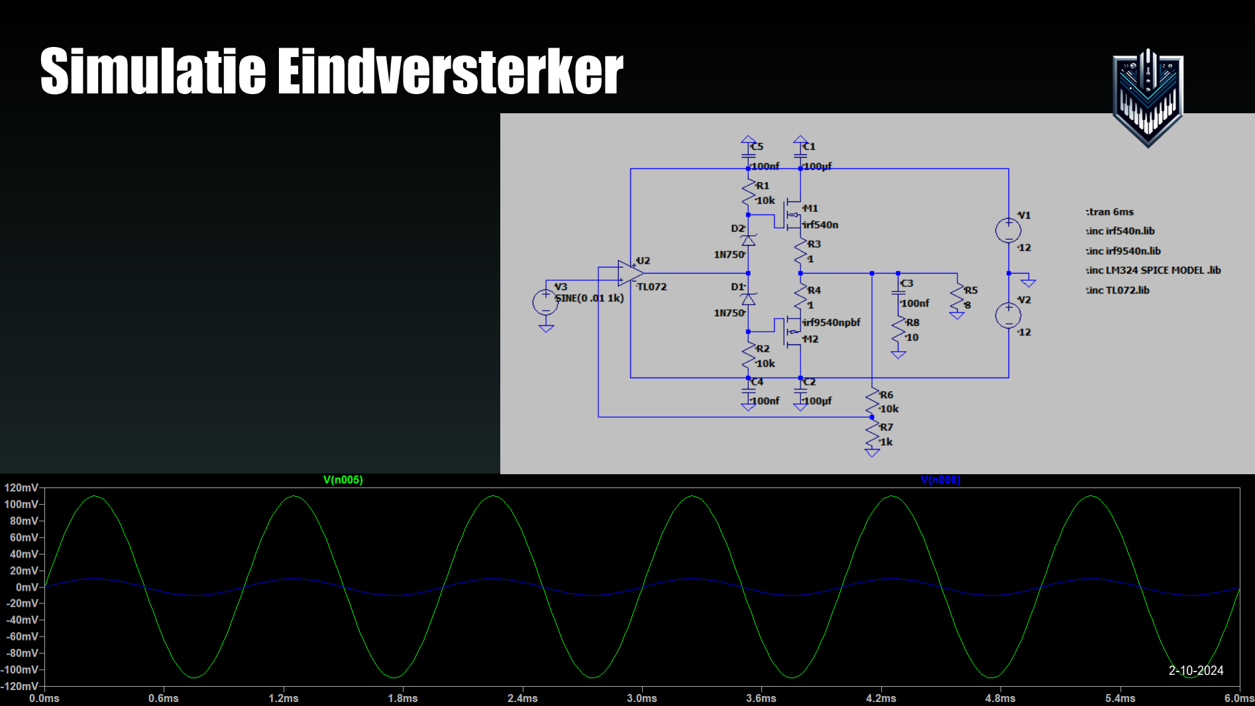
[picture p195: page 6]

# Plan van Eisen, Voeding

Eisen
- Moet verschillende voltages kunnen leveren aan verschillende modules in de synthesizer (functioneel)
- Moet symmetrisch voeding kunnen leveren van minimaal –10 tot +10 Volt (functioneel)
- Moet asymmetrisch voeding kunnen leveren van minimaal +3,3 Volt (functioneel)
- De voeding moet minimaal 80 mAmpère kunnen leveren aan elk van de modules (functioneel)
- De voeding moet aan en uit kunnen worden gezet door de gebruiker (functioneel)
- De voeding mag niet te warm worden (passief, actief) (niet-functioneel)
- Moet een lage rimpelspanning hebben (< 50mV) (niet-functioneel)
- Eindversterker voeding minimaal 0.5 A (functioneel)

Wensen
- Over current protection voor de eindversterker en de voeding (niet-functioneel)
- Beide modules de voeding en de versterker zo energiezuinig maken met minimale verliezen (niet-functioneel)
- Beide modules zo compact mogelijke maken (niet-functioneel)

# Concepten Voeding

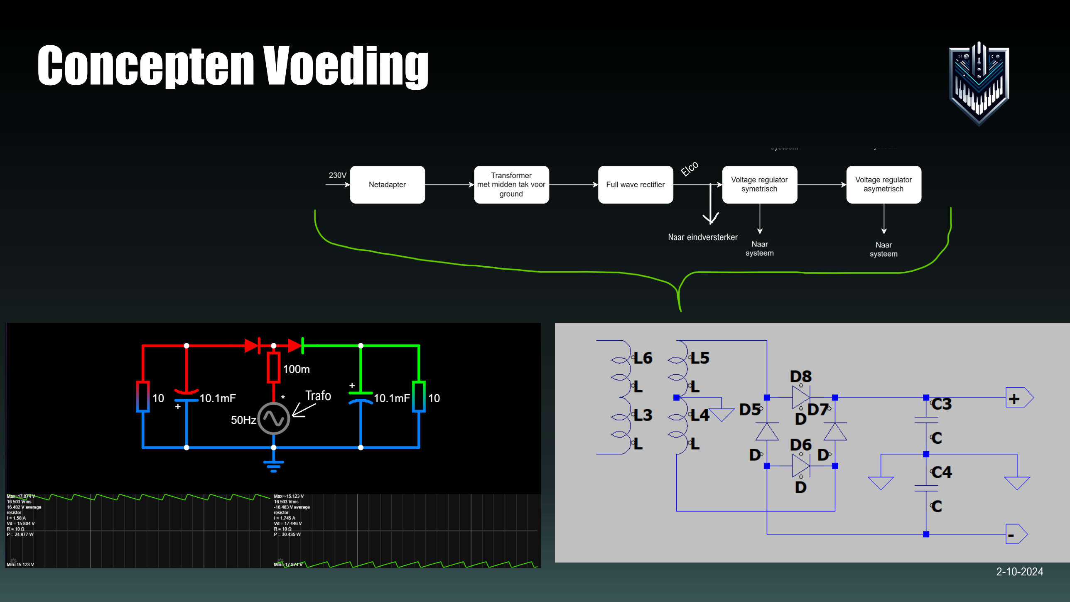
[picture p196: page 8]

Naar eindversterker

Trafo

# Keuze eindversterker


## Voordelen - Weinig tot geen vervorming - Makkelijk te begrijpen

## Nadelen - Er loopt een ruststroom

# Keuze Voeding

Voordelen
- 2 aansluitdraden naar Synthesizer
- Weinig componenten
- Geen geknutsel aan de 230V

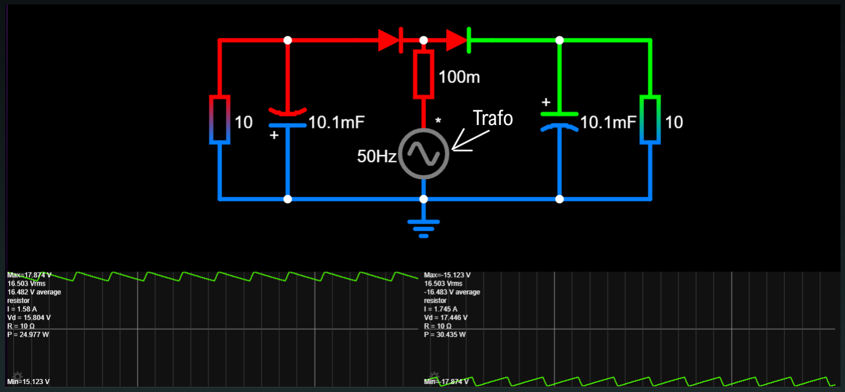
[picture p197: figure]
Trafo

Nadelen
- Veel Elco nodig
