MartijnScheer/Synthesizer/Documentatie 2024-2025/Input/waardes voor voltage en code waarde voor PIB Van Rick Smelt en Patrick van Ommen.pdf

Volt | waarde code | toets op keyboard welke octaaf is het
1,0000 | 310 Check | c | octaaf 1
1,0833 | 338 Check | Db | octaaf 1
1,1667 | 364 Check | d | octaaf 1
1,2500 | 390 check | Eb | octaaf 1
1,3333 | 415 Check | e | octaaf 1
1,4167 | 442 Check | f | octaaf 1
1,5000 | 468 Check | Gb | octaaf 1
1,5833 | 494 Check | g | octaaf 1
1,6667 | 520 Check | Ab | octaaf 1
1,7500 | 546 Check | a | octaaf 1
1,8333 | 572 Check | Bb | octaaf 1
1,9167 | 597 Check | b | octaaf 1
2,0000 | 624 Check | c | octaaf 2
2,0833 | 650 Check | Db | octaaf 2
2,1667 | 676 Check | d | octaaf 2
2,2500 | 702 Check | Eb | octaaf 2
2,3333 | 727 Check | e | octaaf 2
2,4167 | 754 Check | f | octaaf 2
2,5000 | 780 Check | Gb | octaaf 2
2,5833 | 806 Check | g | octaaf 2
2,6667 | 832 Check | Ab | octaaf 2
2,7500 | 858 Check | a | octaaf 2
2,8333 | 884 Check | Bb | octaaf 2
2,9167 | 910 Check | b | octaaf 2
3,0000 | 937 Check | c | octaaf 3

waardes kunnen worden berekent met de volgende formule a = 310 + buttonIndex * 25;
