MartijnScheer/Synthesizer/Documentatie 2024-2025/ADSR+MIXER+VCA/WhatsApp Image 2026-04-22 at 15.32.38.jpeg

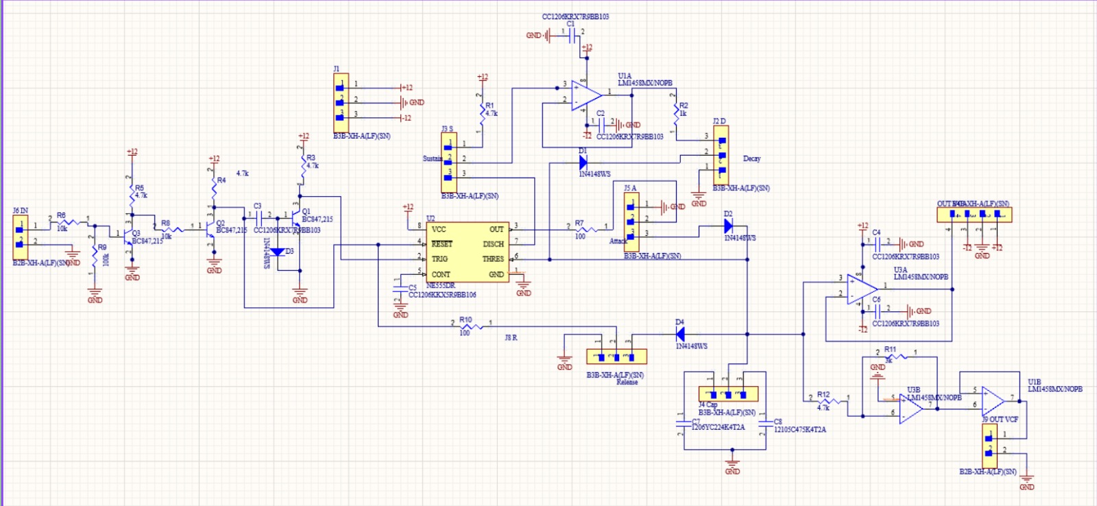
Documentatie 2024-2025/ADSR+MIXER+VCA/WhatsApp Image 2026-04-22 at 15.32.38.jpeg
