MartijnScheer/Synthesizer/Documentatie Minor Project Synthesizer Hidde Huysmans & Martijn Scheer 2026/GitHub Documentatie/Comments.png

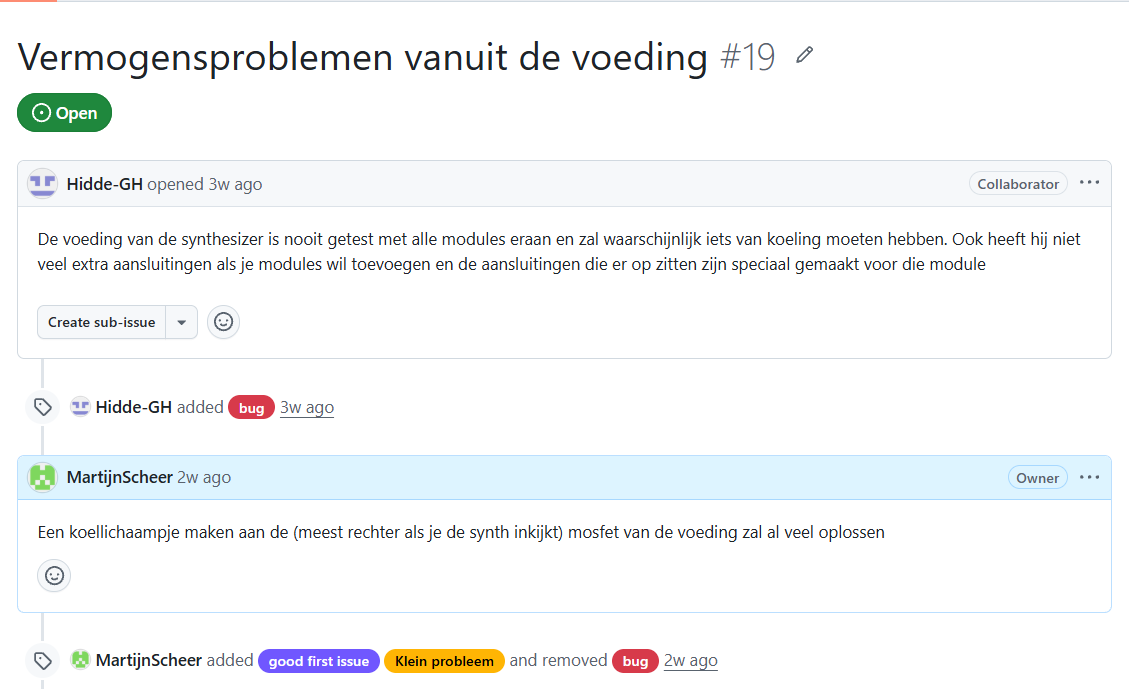
Documentatie Minor Project Synthesizer Hidde Huysmans & Martijn Scheer 2026/GitHub Documentatie/Comments.png
