MartijnScheer/Synthesizer/Documentatie Minor Project Synthesizer Hidde Huysmans & Martijn Scheer 2026/GitHub Documentatie/Compacte voorpagina.png

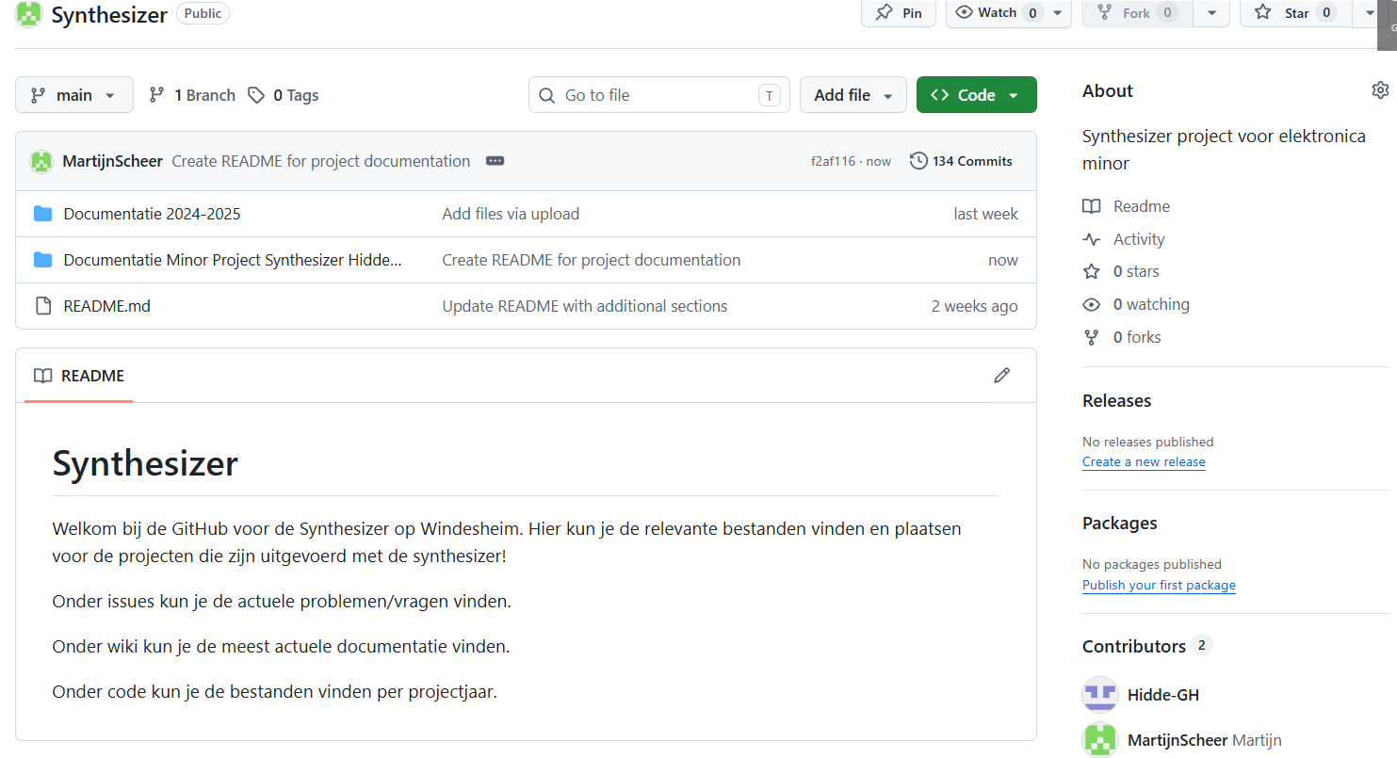
Documentatie Minor Project Synthesizer Hidde Huysmans & Martijn Scheer 2026/GitHub Documentatie/Compacte voorpagina.png
