MartijnScheer/Synthesizer/Documentatie Minor Project Synthesizer Hidde Huysmans & Martijn Scheer 2026/GitHub Documentatie/Wiki.png

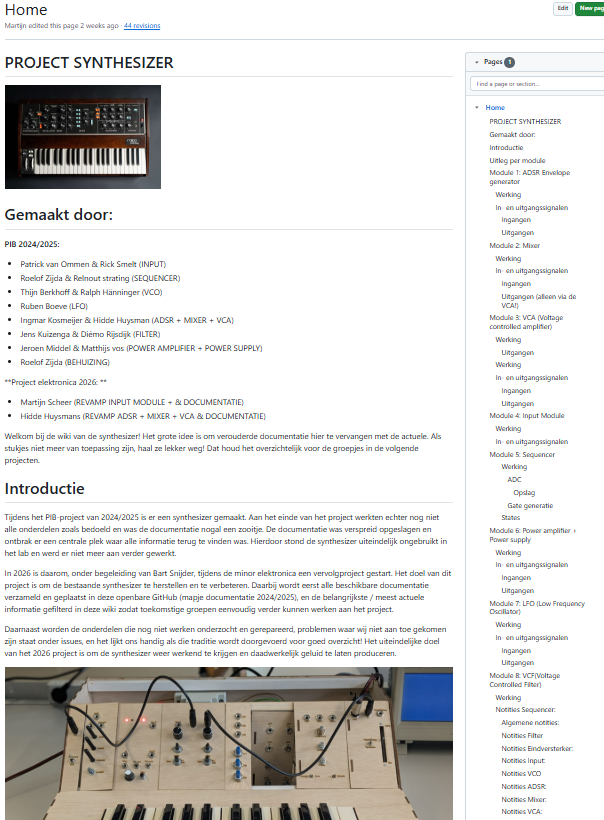
Documentatie Minor Project Synthesizer Hidde Huysmans & Martijn Scheer 2026/GitHub Documentatie/Wiki.png
