MartijnScheer/Synthesizer/Documentatie Minor Project Synthesizer Hidde Huysmans & Martijn Scheer 2026/Vooronderzoekje polyfoon/aantekeningen.png

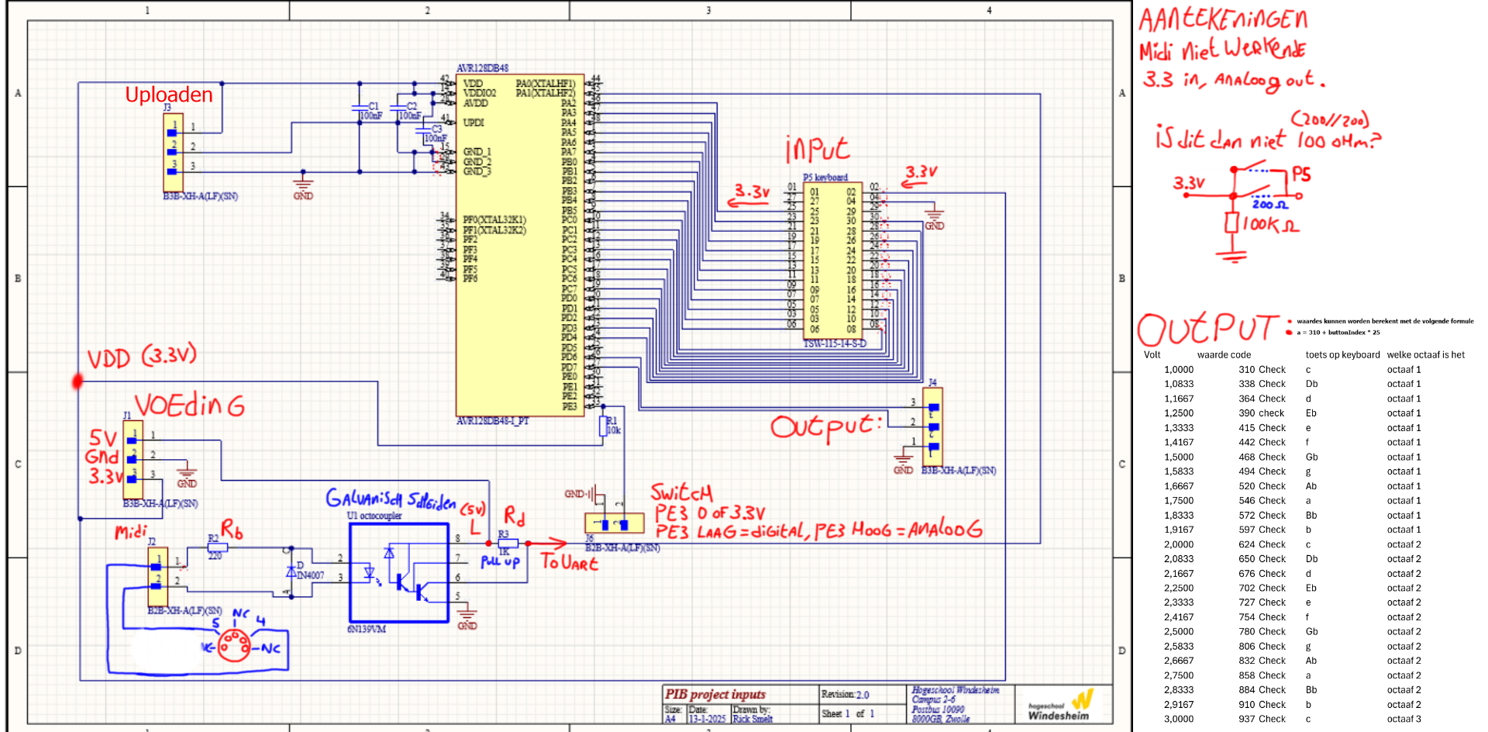
Documentatie Minor Project Synthesizer Hidde Huysmans & Martijn Scheer 2026/Vooronderzoekje polyfoon/aantekeningen.png
