MartijnScheer/Synthesizer/Documentatie 2024-2025/Sequencer/Ombouw_Synth/Assem1_Mixer.SLDASM

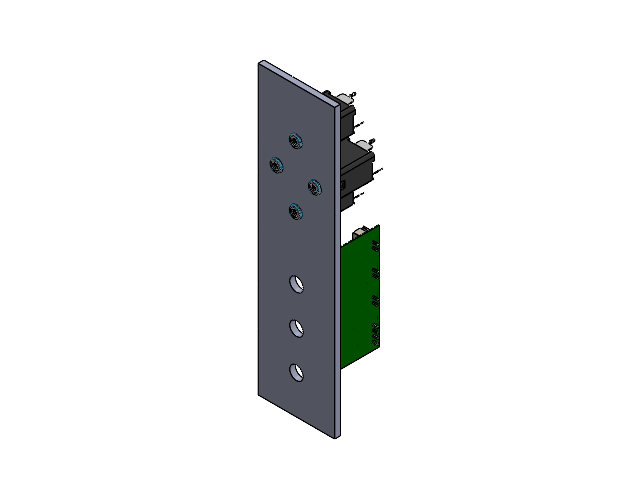
[picture p248: CAD file, 2026-06-26]
Documentatie 2024-2025/Sequencer/Ombouw_Synth/Assem1_Mixer.SLDASM
MIXER panel
53480055_531.stp x 4
50300152_321.stp x 4
50300150_321.stp x 4
50300149_321.stp x 4
50300162_322.stp x 4
1.step x 2
2.step x 2
3.step x 2
Leader.step x 8
Mid_Body.step x 3
Mark.step x 3
Mid_Body-1.step x 2
Mark-2.step x 2
1-4.step x 3
B2B-XH-A.step x 3
JST Logo adjustable.step x 3
1-5.step
2-6.step
Pin1_Triangle.step
JST.step
