MartijnScheer/Synthesizer/Documentatie 2024-2025/Sequencer/Ombouw_Synth/Assem ADSR.SLDASM

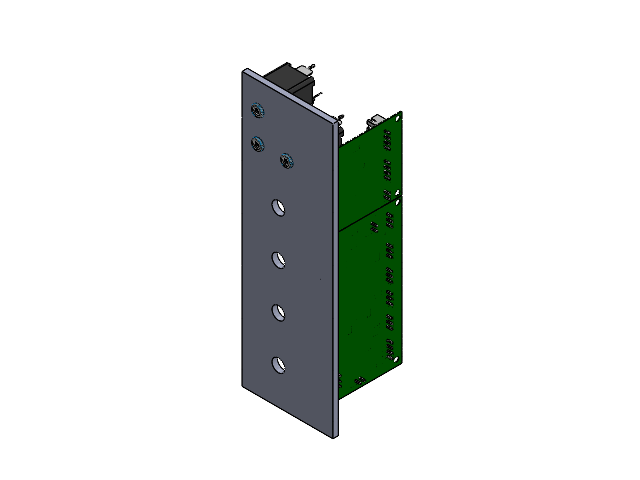
[picture p249: CAD file, 2026-06-26]
Documentatie 2024-2025/Sequencer/Ombouw_Synth/Assem ADSR.SLDASM
ADSR panel
53480055_531.stp x 3
50300152_321.stp x 3
50300150_321.stp x 3
50300149_321.stp x 3
50300162_322.stp x 3
1-4.step x 3
B2B-XH-A.step x 3
JST Logo adjustable.step x 3
Mid_Body.step x 4
Mark.step x 4
Mid_Body-1.step x 4
Mark-2.step x 4
Mid_Body-4.step x 2
Mark-5.step x 2
IC_BODY.step x 2
circle.step x 2
IC_LEG.step x 8
Texas Instruments.step x 2
IC_LEG_MIR8.step x 8
1.step x 5
2.step x 5
3.step x 5
Leader.step x 10
Mid_Body-12.step x 2
Mark-13.step x 2
IC_BODY-15.step x 3
IC_LEG-16.step x 9
Nexperia.step x 3
Body.step x 5
Pins.step x 5
Marking.step x 5
JST Logo.step x 5
1-5.step
2-6.step
Pin1_Triangle.step
JST.step
Leader-22.step x 2
Leader-25.step x 4
1-26.step
2-27.step
AVX Logo 2.step
1-28.step
2-29.step
AVX_Logo.step
Body_1.step
side.step x 2
Yageo Logo.step
1_1.step x 2
2_1.step x 2
3_1.step x 2
MANIFOLD_SOLID_BREP_2784.step
MANIFOLD_SOLID_BREP_2935.step
MANIFOLD_SOLID_BREP_3086.step
MANIFOLD_SOLID_BREP_3237.step
BODY_M08A_35.step
LEAD_M08A_57.step x 8
Mid_Body_1.step x 8
Mark_1.step x 8
Mid_Body-1_1.step x 4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
