MartijnScheer/Synthesizer/Documentatie 2024-2025/Sequencer/Ombouw_Synth/PIB Synthesizer Eindversterker.SLDASM

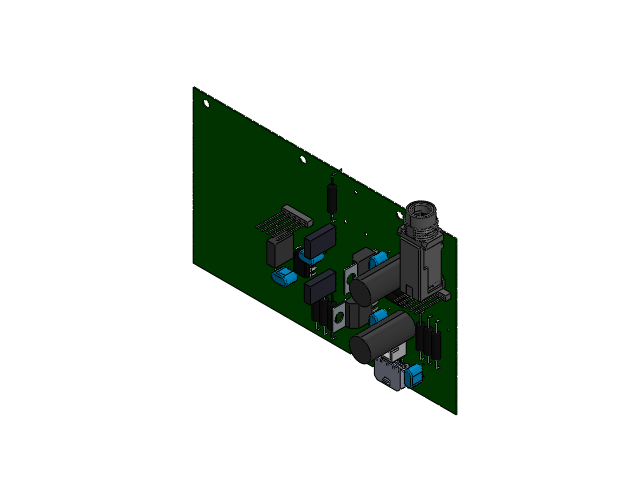
[picture p250: CAD file, 2026-06-26]
Documentatie 2024-2025/Sequencer/Ombouw_Synth/PIB Synthesizer Eindversterker.SLDASM
Body.step x 2
Pins.step x 2
Marking.step x 2
JST Logo.step x 2
Extruded.step x 2
Extruded-0.step x 10
IC_BODY.step
circle.step
IC_LEG.step x 4
Texas Instruments.step
IC_LEG_MIR8.step x 4
Mid_Body-1.step x 2
Mark-2.step x 2
Mid_Body-4.step x 4
Mark-5.step x 4
Mid_Body-12.step x 2
Mark-13.step x 2
Mid_Body.step
Mark.step
Mid_Body-7.step
Mark-8.step
Tab.step
Body-10.step
PinsArray.step
IC_BODY-15.step x 3
IC_LEG-16.step x 9
Nexperia.step x 3
630BT-1.step
630LS-1.step
PRT0003-1.step
630C2-1.step
630GZ-1.step
630-31-1.step
1-26.step
2-27.step
AVX Logo 2.step
1-28.step
2-29.step
AVX_Logo.step
1-10.step x 5
2.step x 5
3.step x 5
body_1.step
side.step x 2
Yageo Logo.step
