MartijnScheer/Synthesizer/Documentatie 2024-2025/Sequencer/Ombouw_Synth/sequencer pcb v2.SLDASM

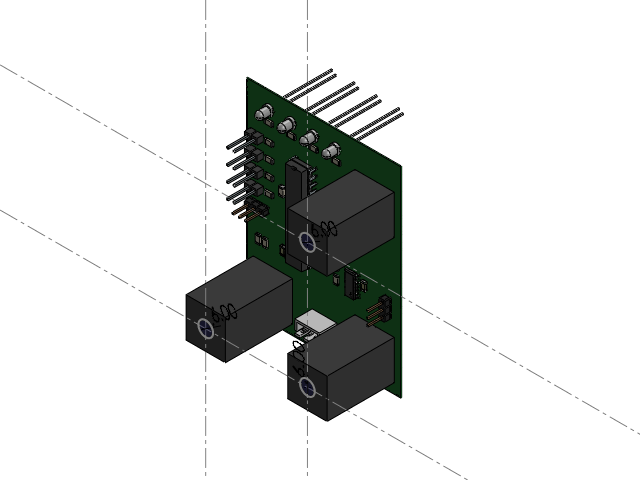
[picture p251: CAD file, 2026-06-26]
Documentatie 2024-2025/Sequencer/Ombouw_Synth/sequencer pcb v2.SLDASM
Body_1.step
Pins_1.step
Marking_1.step
JST Logo_1.step
IC_BODY.step
circle.step
IC_LEG.step x 7
STMicroelectronics.step
IC_LEG_MIR8.step x 7
Extruded_1.step x 2
Extruded-0_1.step x 4
Extruded-1.step x 2
Extruded-2.step x 4
Extruded-3.step x 4
Extruded-4.step x 8
Extruded-5.step x 8
Extruded-6.step x 4
61300311121-7.step x 2
6130xx11121_PIN.step x 6
Body-8.step x 3
Leads_1.step x 3
Body-9.step x 4
LeadsArray.step x 4
Body-10_1.step
PinsArrayLR.step
15103xxx.step x 4
Cap_KEMET_C1206C472K4RACTU_eec.step x 4
Cap_KEMET_C1206C472K4RACTU_eec-11.step x 4
Cap_KEMET_C1206C472K4RACTU_eec-12.step x 4
Extruded-13_1.step x 6
Extruded-14.step x 3
