MartijnScheer/Synthesizer/Documentatie Minor Project Synthesizer Hidde Huysmans & Martijn Scheer 2026/GitHub Documentatie/Issues.png

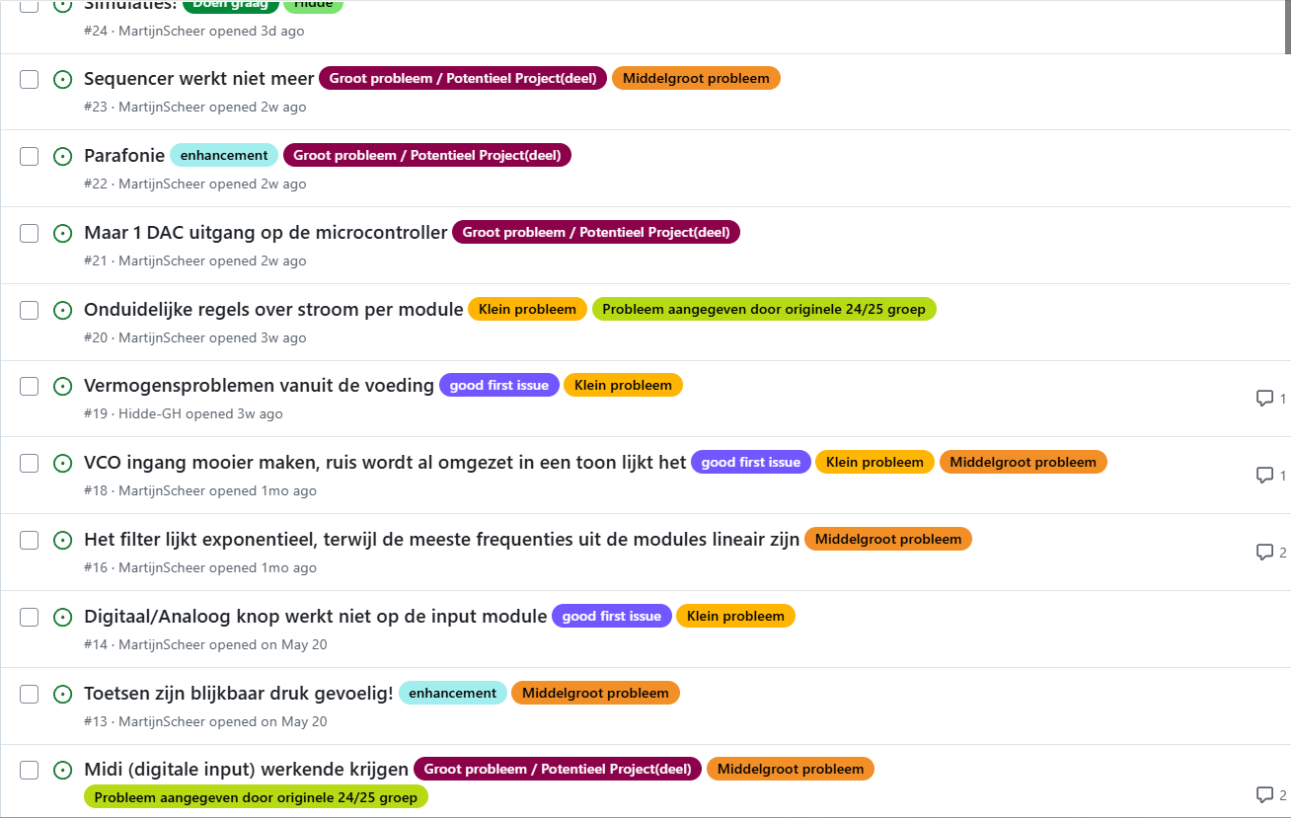
Documentatie Minor Project Synthesizer Hidde Huysmans & Martijn Scheer 2026/GitHub Documentatie/Issues.png
