MartijnScheer/Synthesizer/Documentatie 2024-2025/Filter/VCF_Project_Jens_Kuzienga_1175555_Altium.pdf

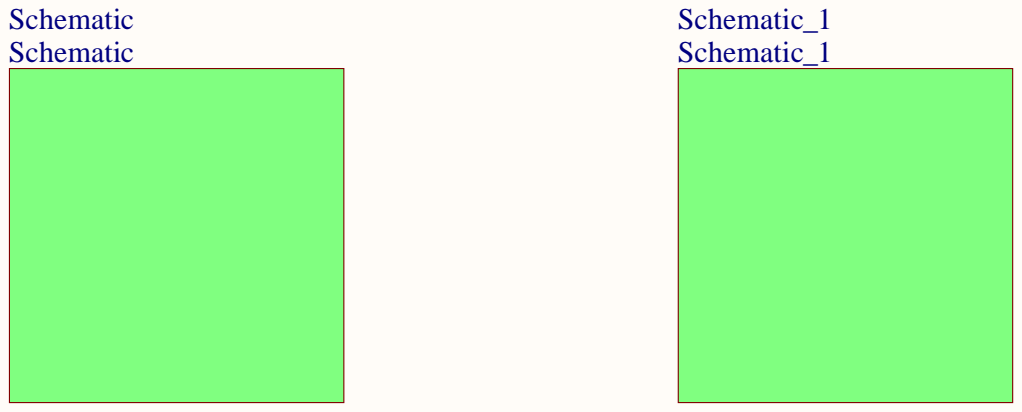
[picture p253: page 1]

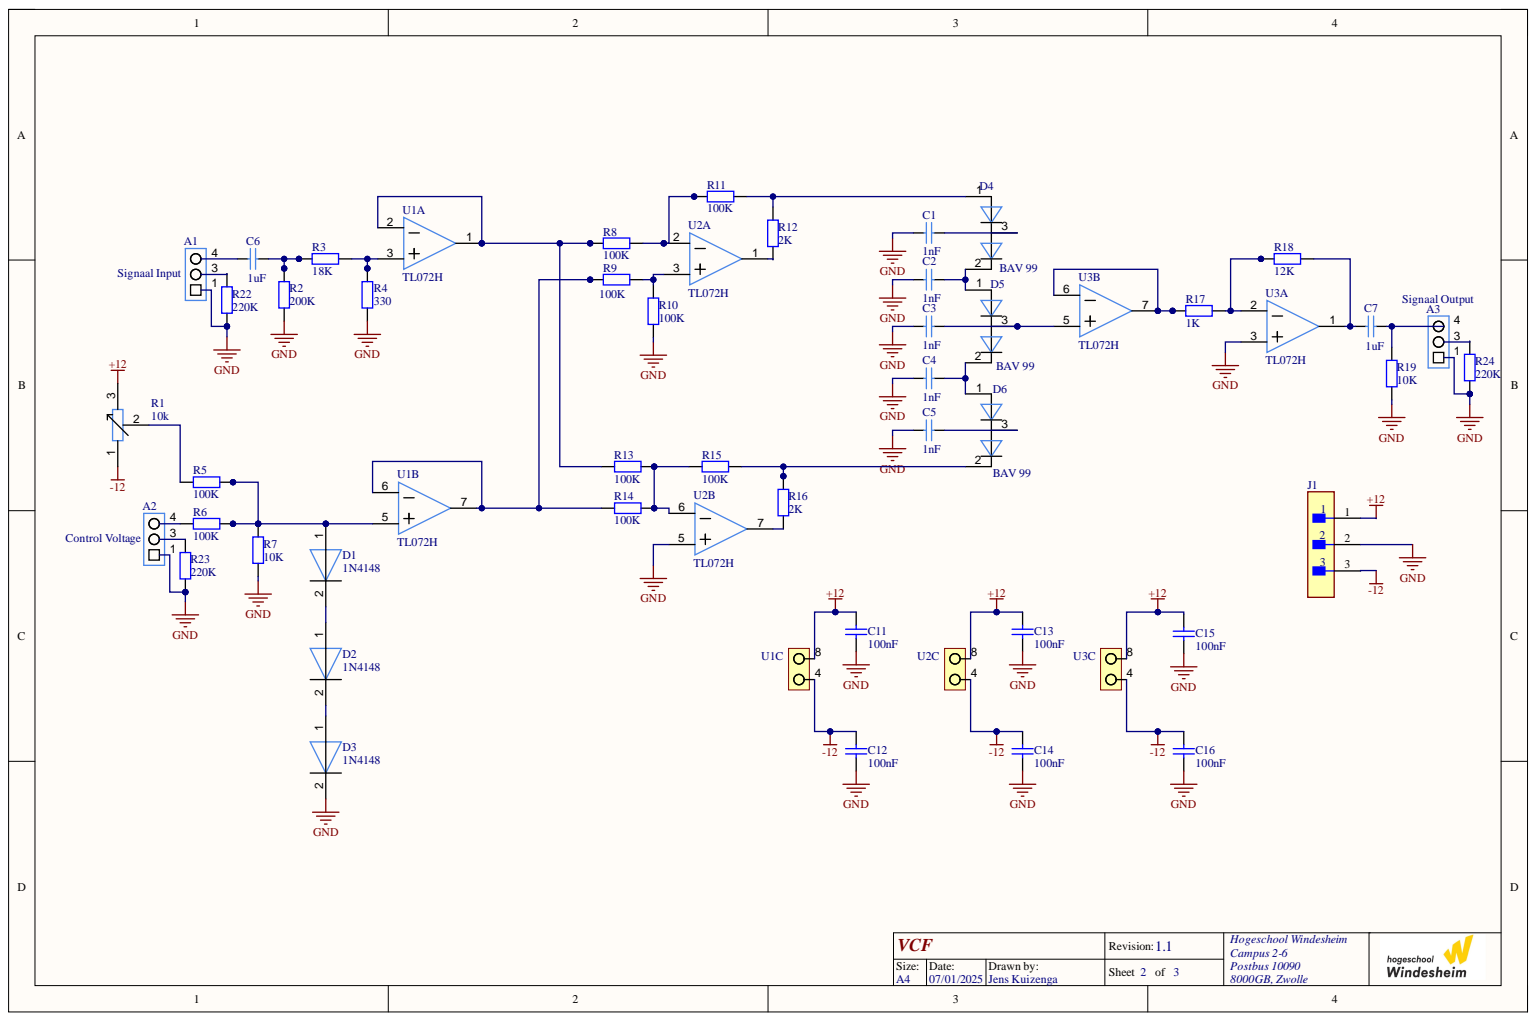
[picture p254: page 2]

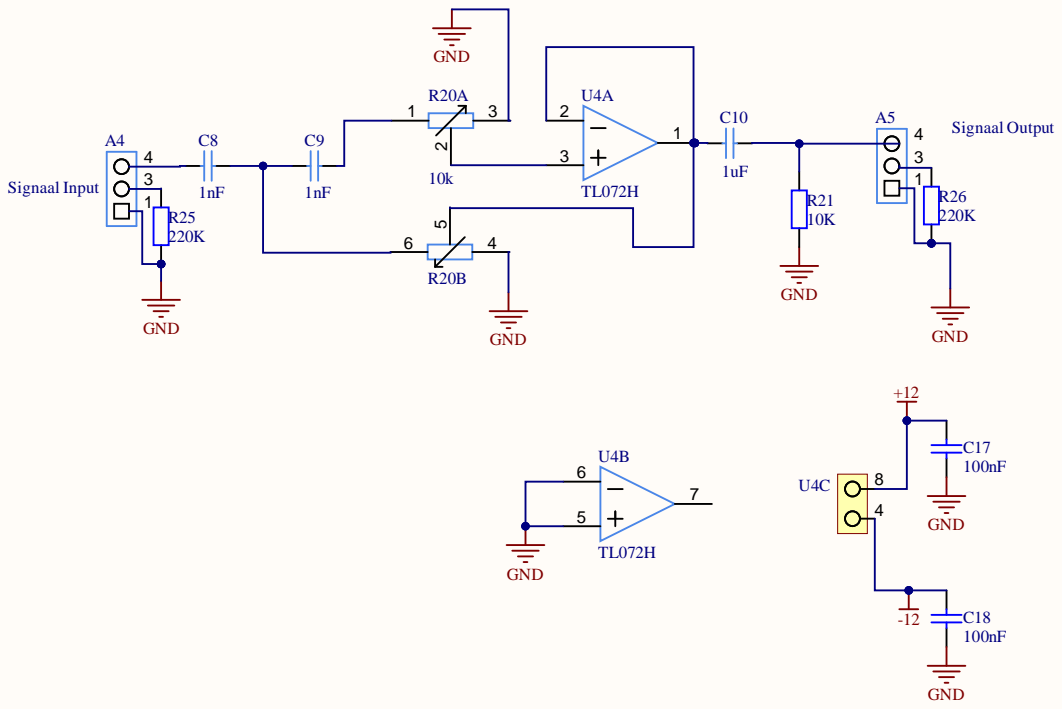
[picture p255: page 3]

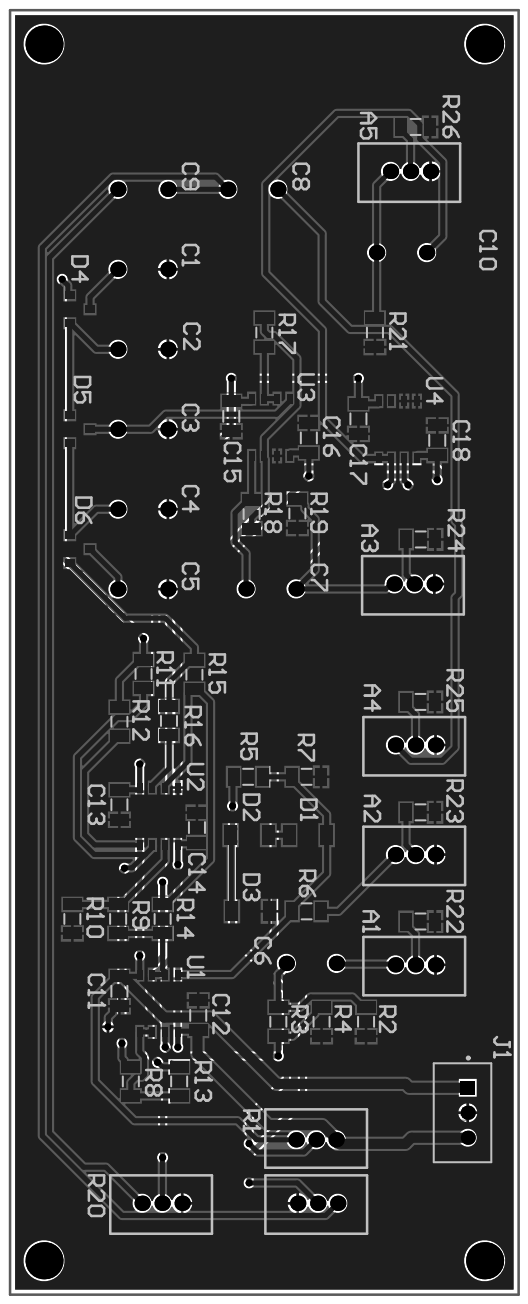
[picture p256: page 4]

Comment | Description | Designator | Footprint | LibRef | Quantity
Audiojack | Audiojack3.5mm | A1, A2, A3, A4, A5 | JSTconnector Audio jack3.5mm | Audiojack | 5
1nF | Condensator | C1, C2, C3, C4, C5, C8, C9 | Condensator | Condensator | 7
1uF | Condensator | C6, C7, C10 | Condensator | Condensator | 3
100nF | SMDCapacitor 1206 | C11, C12, C13, C14, C15, C16, C17, C18 | C1206 | Capacitor_1206 | 8
1N4148 | Small signal fast switchingdiode | D1, D2, D3 | 1N4148small signal diode | 1N4148 | 3
BAV99 | Small signal diode. 2in onecase | D4, D5, D6 | BAV99 | BAV99 | 3
B3B-XH-A(LF)(SN) | CONNHEADERVERT 3POS2.5MM | J1 | FP-B3B-XH-A_LF_SN-MFG | CMP-17439-000014-3 | 1
10k | 10kPotmeter mono | R1 | JSTconnector 10kPot mono | Potentiometer_0 | 1
200K | SMDResistor 1206 | R2 | R1206 | Resistor_1206 | 1
18K | SMDResistor 1206 | R3 | R1206 | Resistor_1206 | 1
330 | SMDResistor 1206 | R4 | R1206 | Resistor_1206 | 1
100K | SMDResistor 1206 | R5, R6, R8, R9, R10, R11, R13, R14, R15 | R1206 | Resistor_1206 | 9
10K | SMDResistor 1206 | R7, R19, R21 | R1206 | Resistor_1206 | 3
2K | SMDResistor 1206 | R12, R16 | R1206 | Resistor_1206 | 2
1K | SMDResistor 1206 | R17 | R1206 | Resistor_1206 | 1
12K | SMDResistor 1206 | R18 | R1206 | Resistor_1206 | 1
10k | 10kPotmeter stereo | R20 | JSTconnector 10kPot Stereo | Potentiometer_1 | 1
220K | SMDResistor 1206 | R22, R23, R24, R25, R26 | R1206 | Resistor_1206 | 5
TL072H | TwoopampsinoneIC | U1, U2, U3, U4 | TL072H | TL072H | 4
