MartijnScheer/Synthesizer/Documentatie 2024-2025/Power amplifier + Power supply/Ontwerp/PIB Synthesizer Eindversterker.pdf

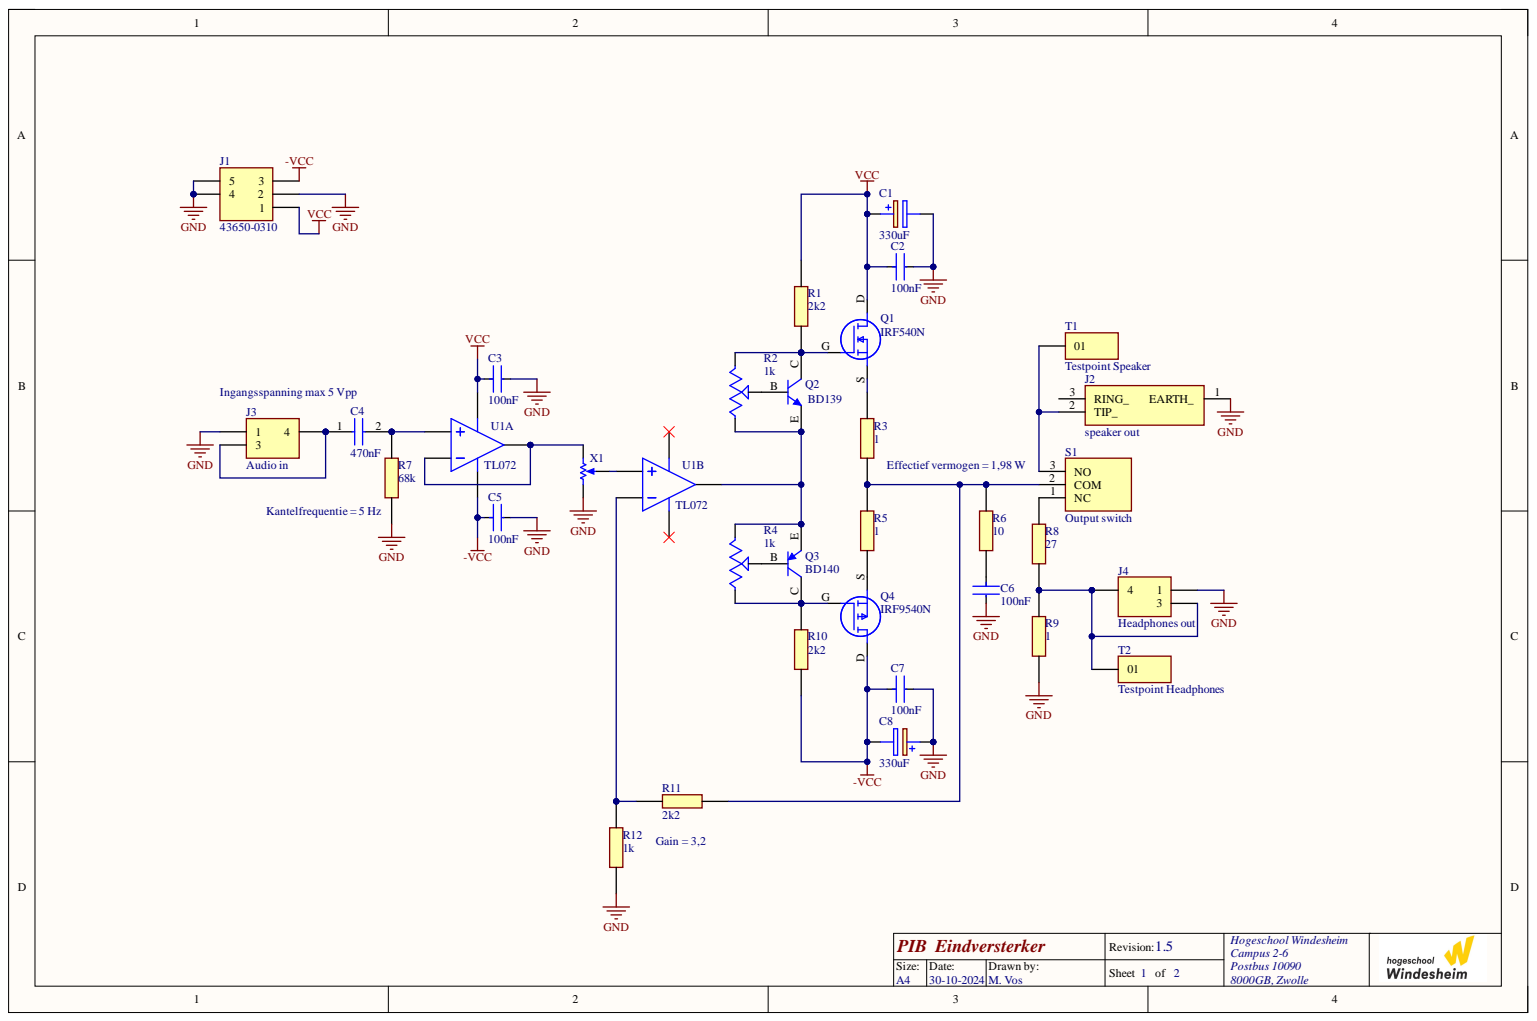
[picture p257: page 1]

Output switch Kantelfrequentie = 5 Hz

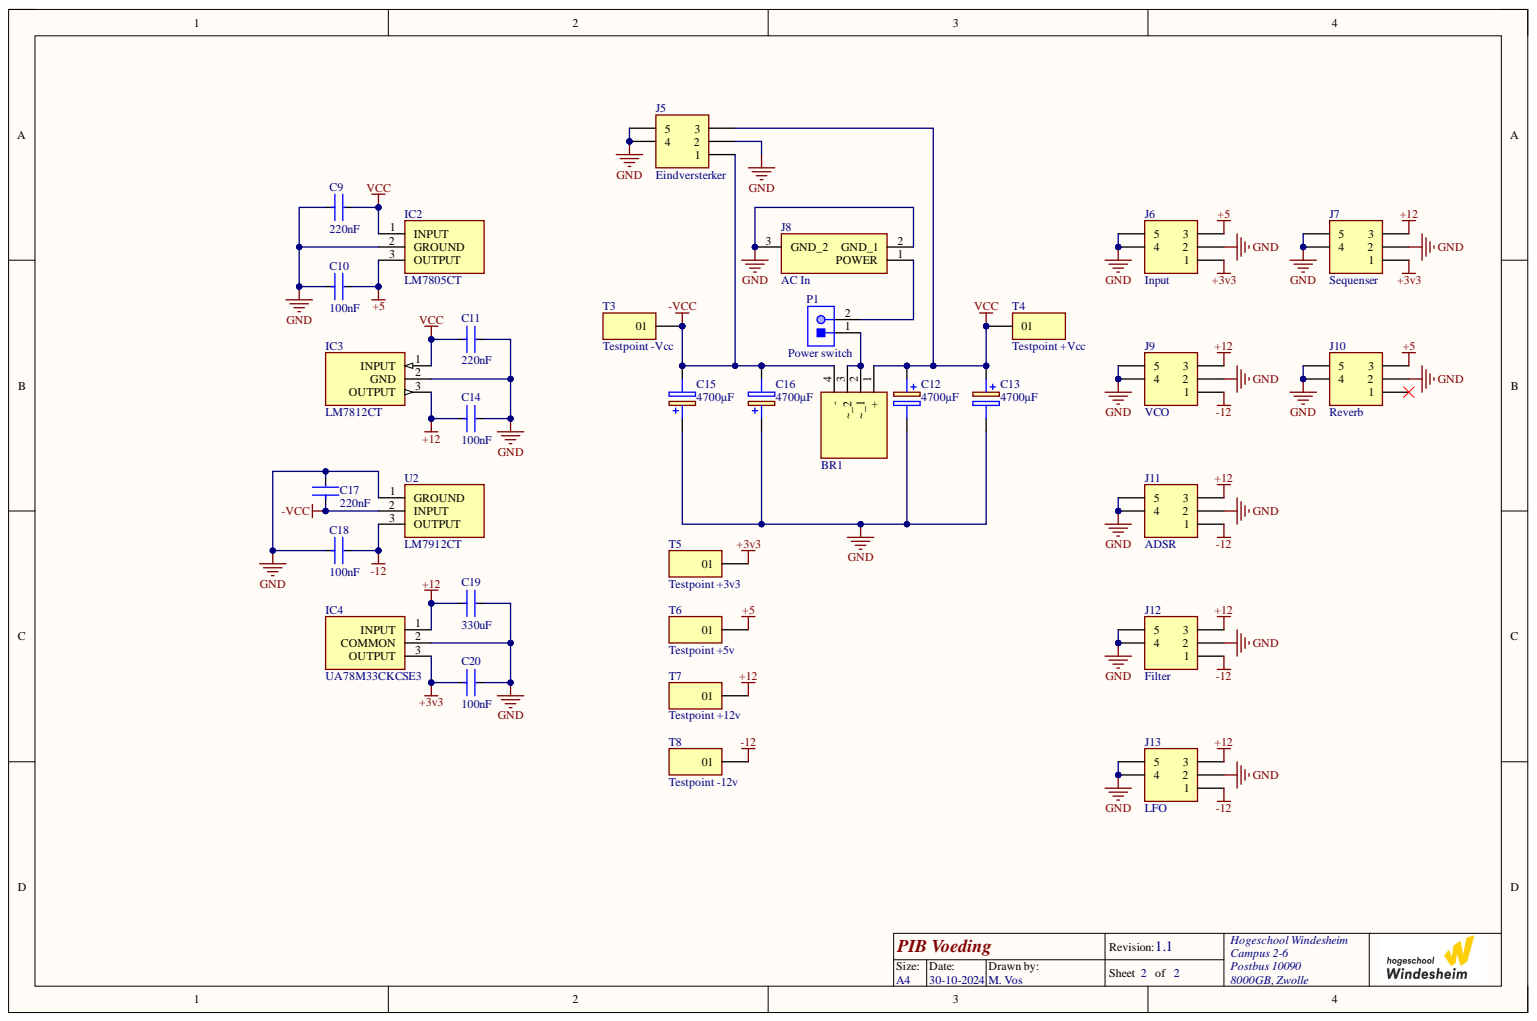
[picture p258: page 2]
