MartijnScheer/Synthesizer/Documentatie 2024-2025/Power amplifier + Power supply/PCB Files/PIB Synthesizer Eindversterker.pdf

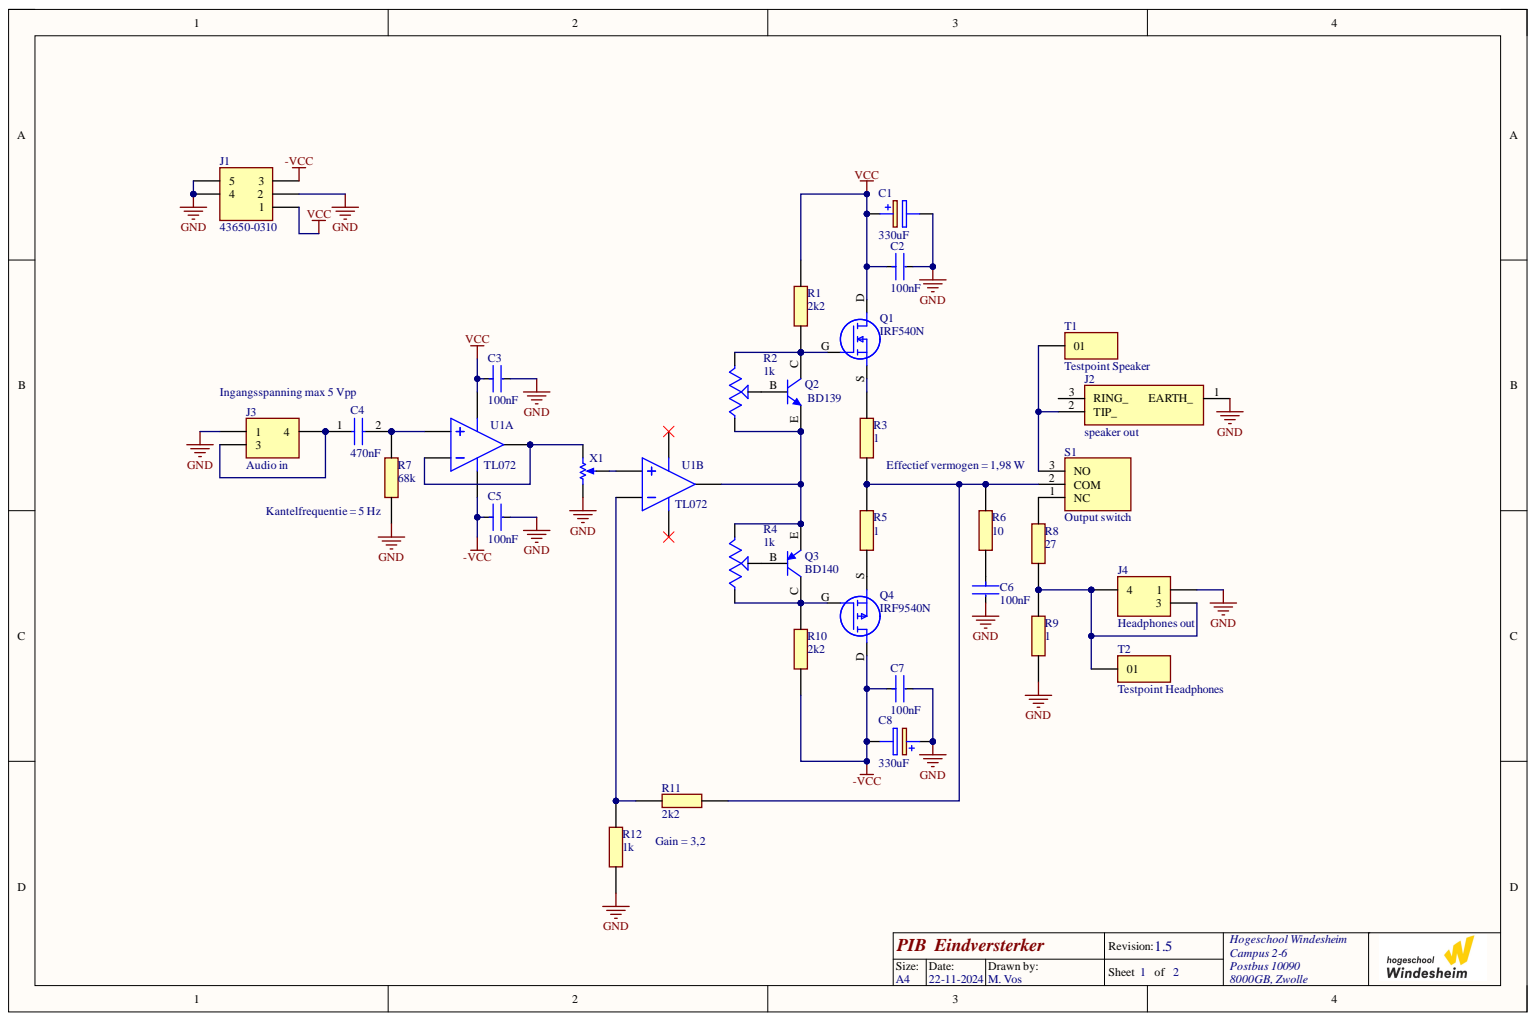
[picture p259: page 1]

Output switch Kantelfrequentie = 5 Hz

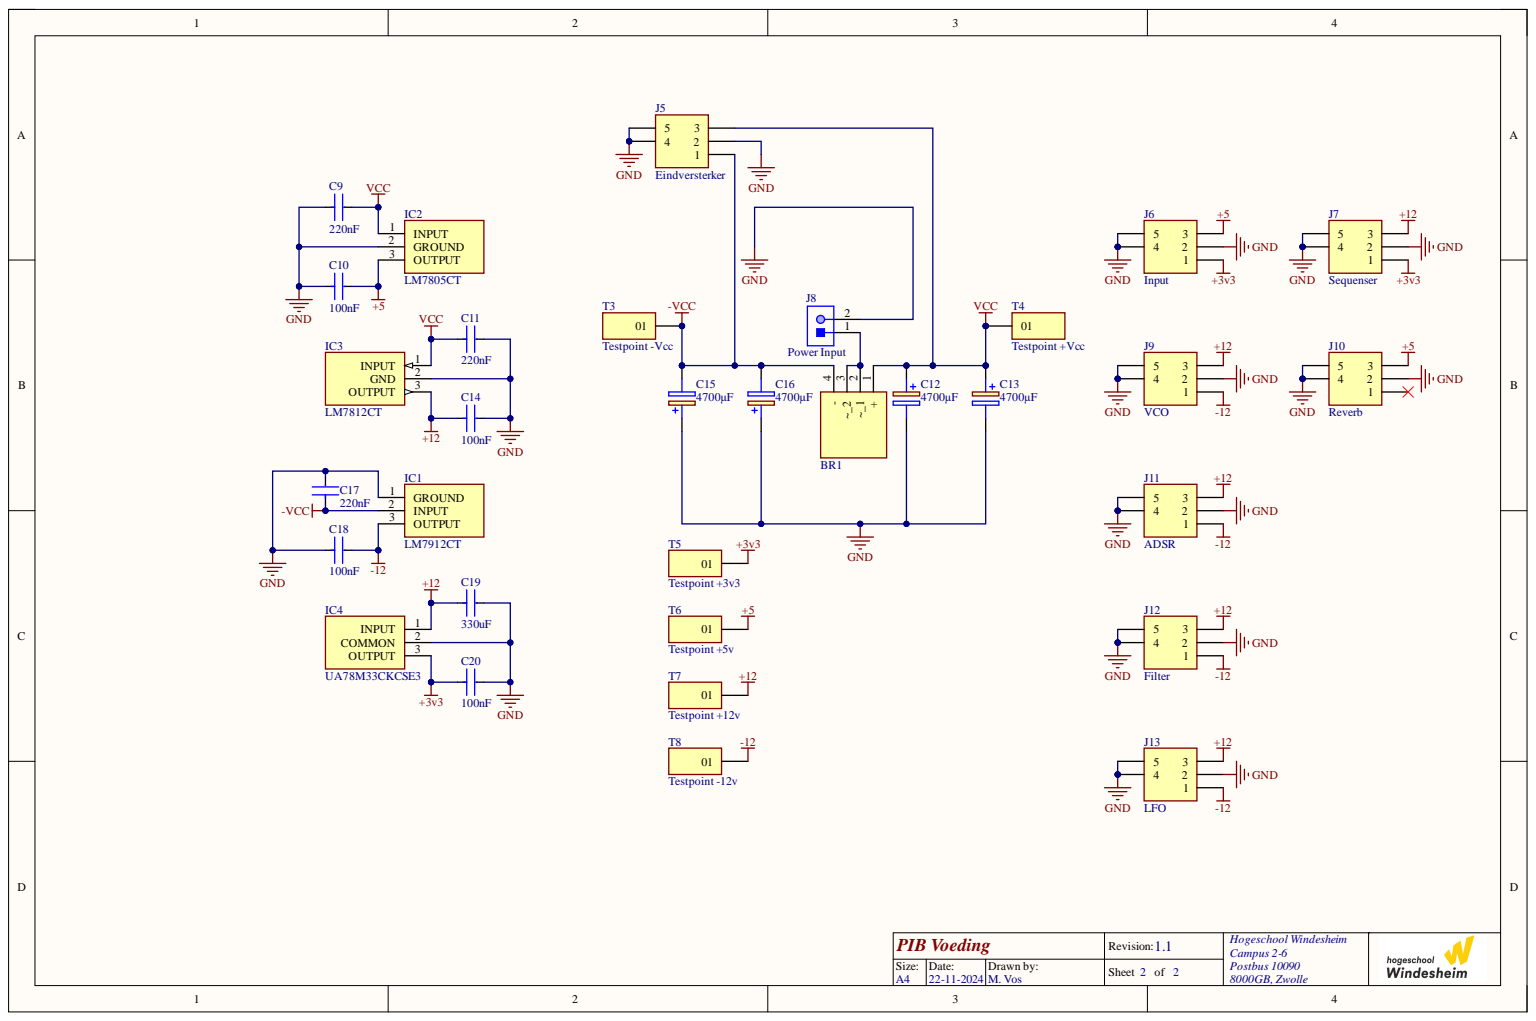
[picture p260: page 2]

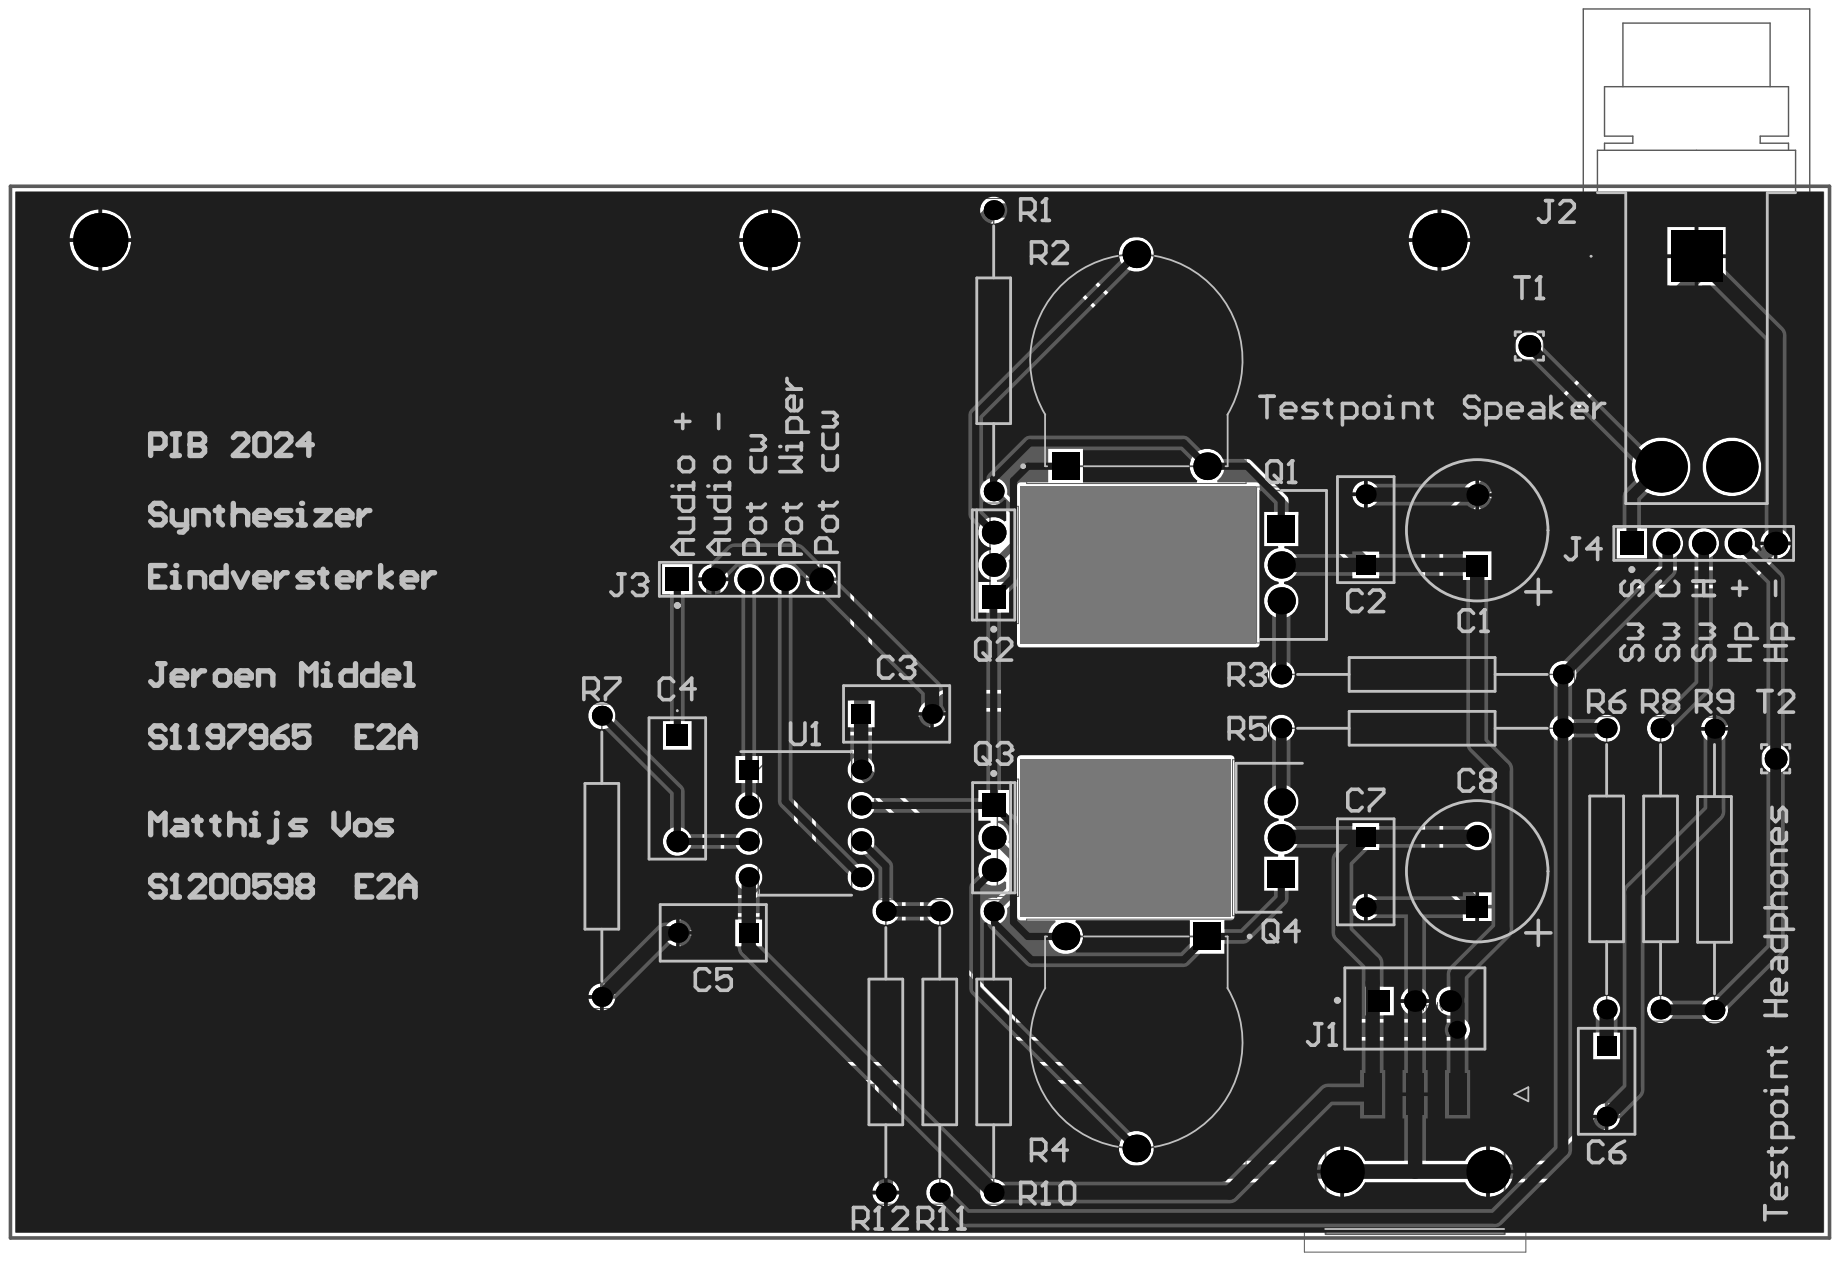
[picture p261: page 3]

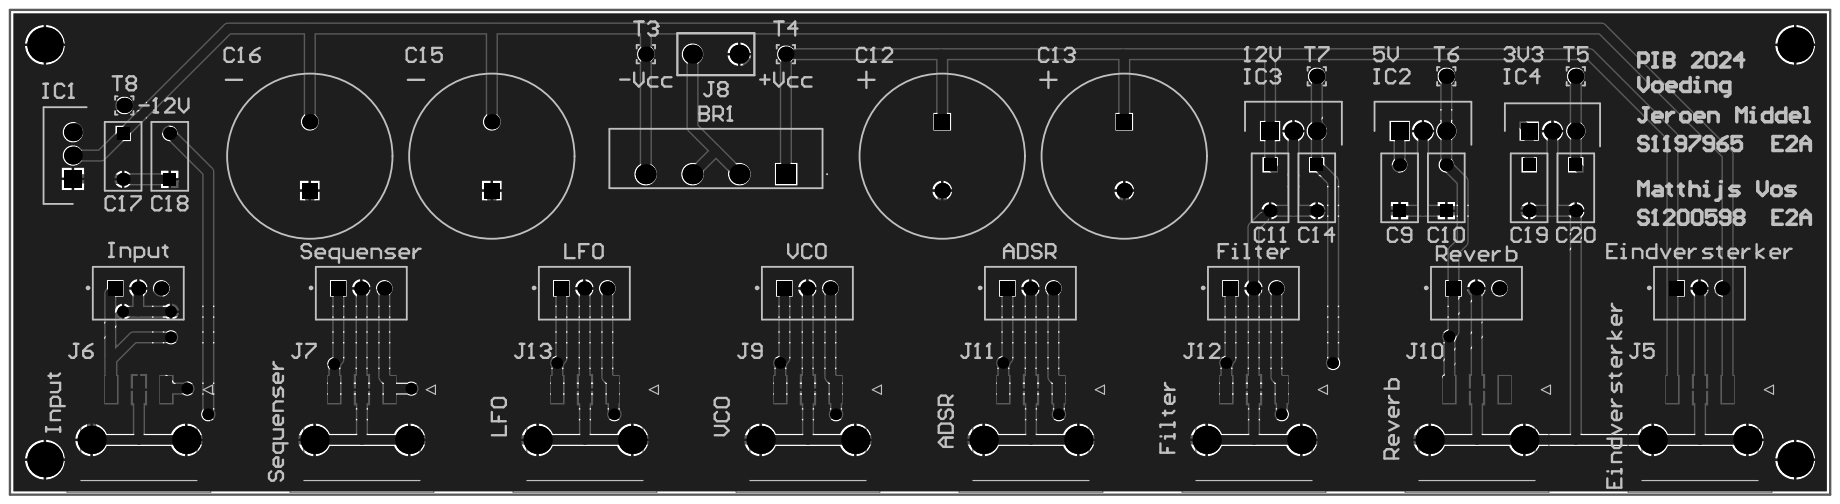
[picture p262: page 4]
