MartijnScheer/Synthesizer/Documentatie Minor Project Synthesizer Hidde Huysmans & Martijn Scheer 2026/ADSR aanpak/Sims/4_channel_lm324_test_1.0.asc

U1: LM324
U2: LM324
U3: LM324
U4: LM324
Named nets: IN1-, IN1+, -VEE, +VCC, IN2-, IN3+, IN3-, IN4-, IN2+, IN4+, OUT1, OUT2, OUT3, OUT4
