MartijnScheer/Synthesizer/Documentatie 2024-2025/VCO/VCO sim Thijn Berkhoff.asc

C1: cap; 100nF
C2: cap; 100nF
C3: cap; 100nF
D1: diode; 1N4148
D2: diode; 1N4148
pot5K: res; 3K
pot100K: res; 50K
Q1: npn; BC547B
Q2: pnp; BC557B
R1: res; 33K
R2: res; 100K
R3: res; 10K
R4: res; 330
R5: res; 18K
R6: res; 10K
R7: res; 10K
R8: res; 82K
R9: res; 10K
R10: res; 10K
trimpot500: res; 330
U1: UniversalOpAmp5
U2: UniversalOpAmp5
U3: UniversalOpAmp5
U4: UniversalOpAmp5
U5: UniversalOpAmp5
U6: UniversalOpAmp5
V1: voltage; 12
V2: voltage; 12
Vin: voltage; 2V
Named nets: 0, -12, +12, Sqrout, invsawout, sawout
.tran 10ms
op het moment is C1 47, 100 of 220nF
offset
input
fine
Dit is het elektrisch schema van de VCO die op het breadbord gemonteerd is.
Dit is alleen het oscillatorgedeelte, de frequentie op de uitgang komt niet 
overeen met de realiteit. Dit zou met de slewrate vd opamps te maken kunnen hebben
of misschien een fout in de schakeling.
 
De fout is gevonden, de PNP BJT stond in het 
breadbord verkeerd om.
Op het breadbord worden de amplitudes met spanningsdelers binnen de eisen gezet
van +/- 2,5V. De grote pieken op de zaagtanden zijn in de realiteit niet aanwezig.
