MartijnScheer/Synthesizer/Documentatie Minor Project Synthesizer Hidde Huysmans & Martijn Scheer 2026/ADSR aanpak/Sims/transistortrap ADSR.asc

C1: cap; 10nF
D1: diode; 1N4148
Q1: npn; BC547C
Q2: npn; BC547C
Q3: npn; BC547C
R1: res; 10k
R2: res; 100k
R3: res; 10k
R4: res; 4.7k
R5: res; 4.7k
R6: res; 4.7k
V1: voltage; PULSE(0 5 0 1u 1u 5 10 3); AC 1
Named nets: 0, In, Out_Q1, Out_Q2, Out_Q3, TRIGGER, RESET
.tran 0 10 0 0.01
